stawiski/open-ring/images/charger-pcb-1.jpg

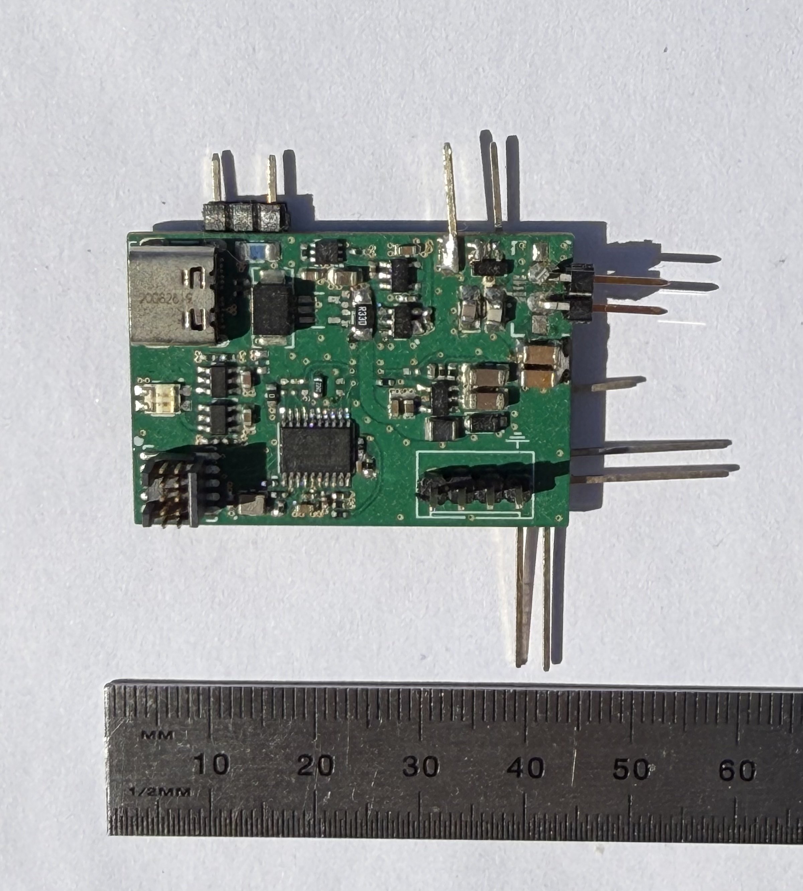
images/charger-pcb-1.jpg
