stawiski/open-ring/images/charger-pcb-2.jpg

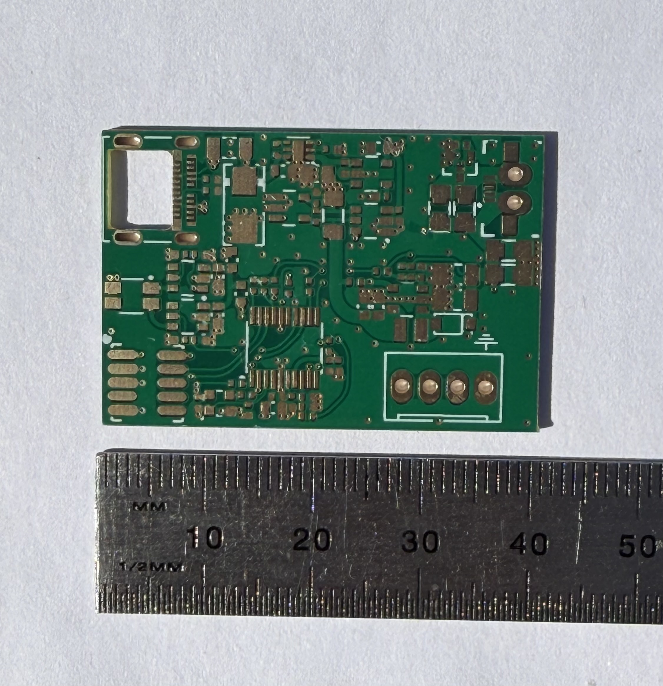
images/charger-pcb-2.jpg
