stawiski/open-ring/images/prototype-charger-2.jpg

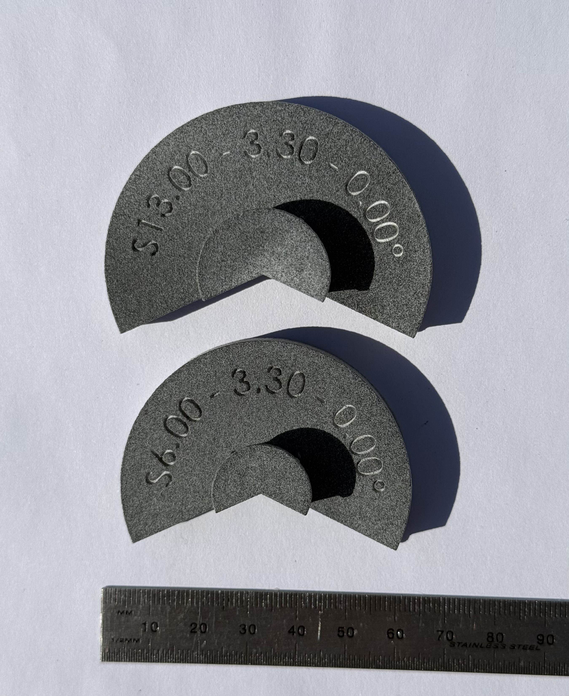
images/prototype-charger-2.jpg
