stawiski/open-ring/images/ring-antenna-w3008.jpg

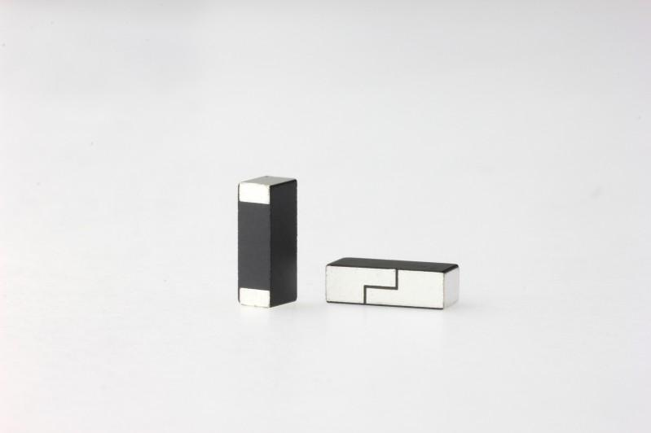
images/ring-antenna-w3008.jpg
