stawiski/open-ring/images/ring-battery-grepow-1.png

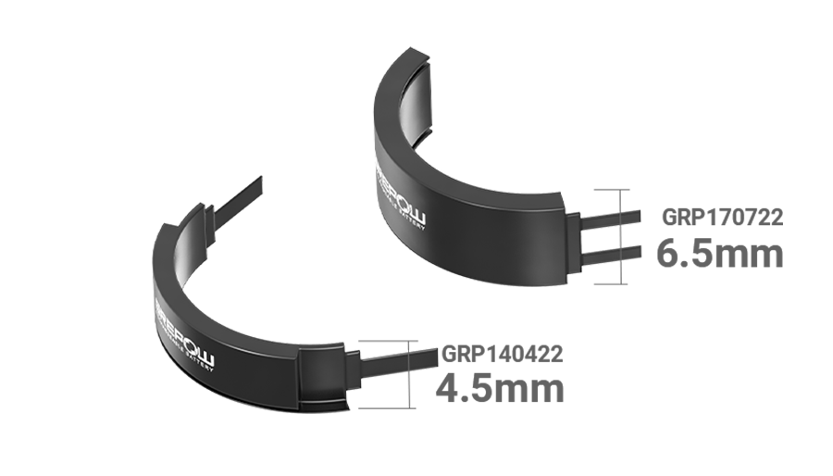
images/ring-battery-grepow-1.png
