stawiski/open-ring/images/ring-battery-grepow-2.jpg

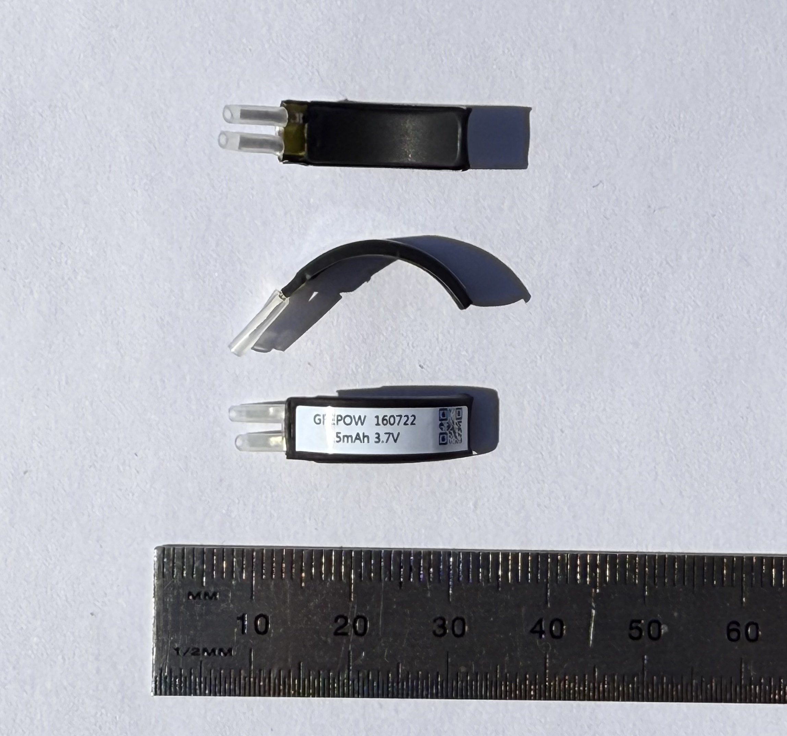
images/ring-battery-grepow-2.jpg
