stawiski/open-ring/images/ring-touch-sensor-prototypes-1.png

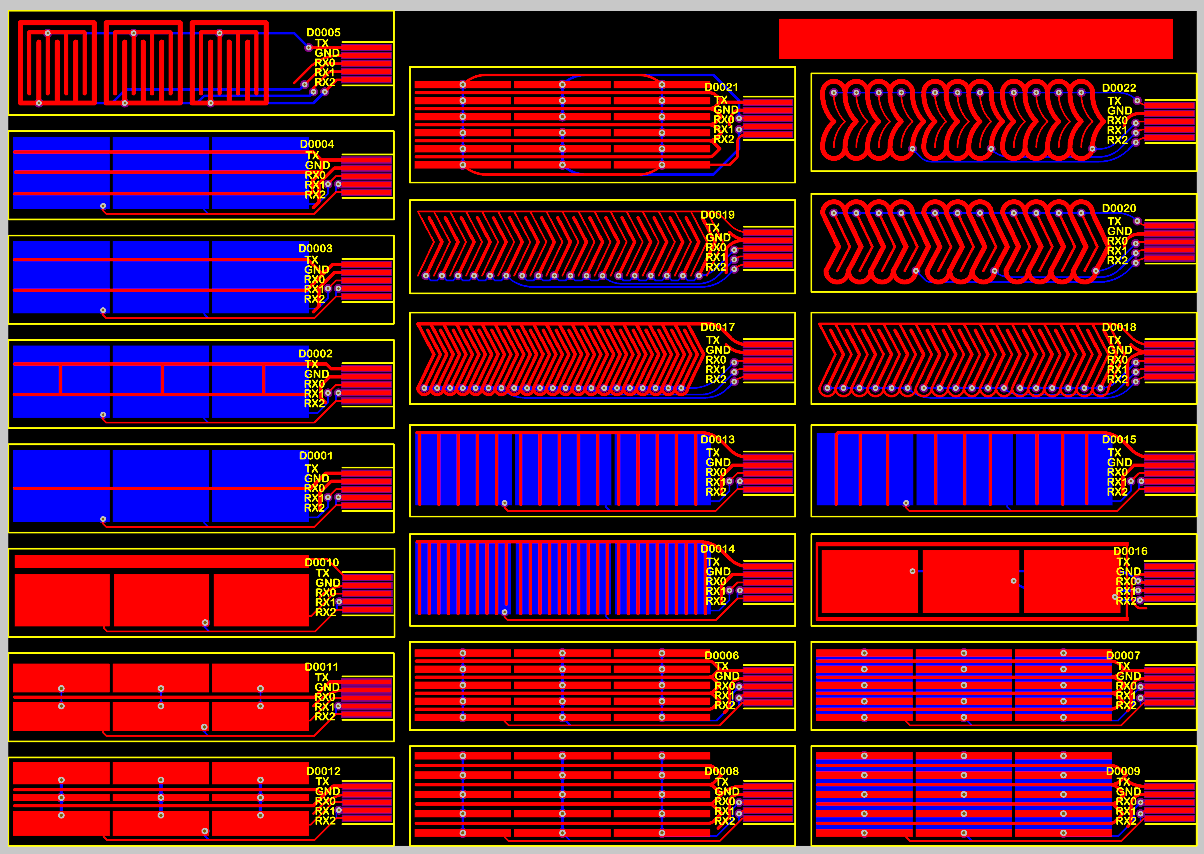
images/ring-touch-sensor-prototypes-1.png
