stawiski/open-ring/hardware-prototypes/ring-dev-board/docs/Connector Molex 545480433_sd.pdf

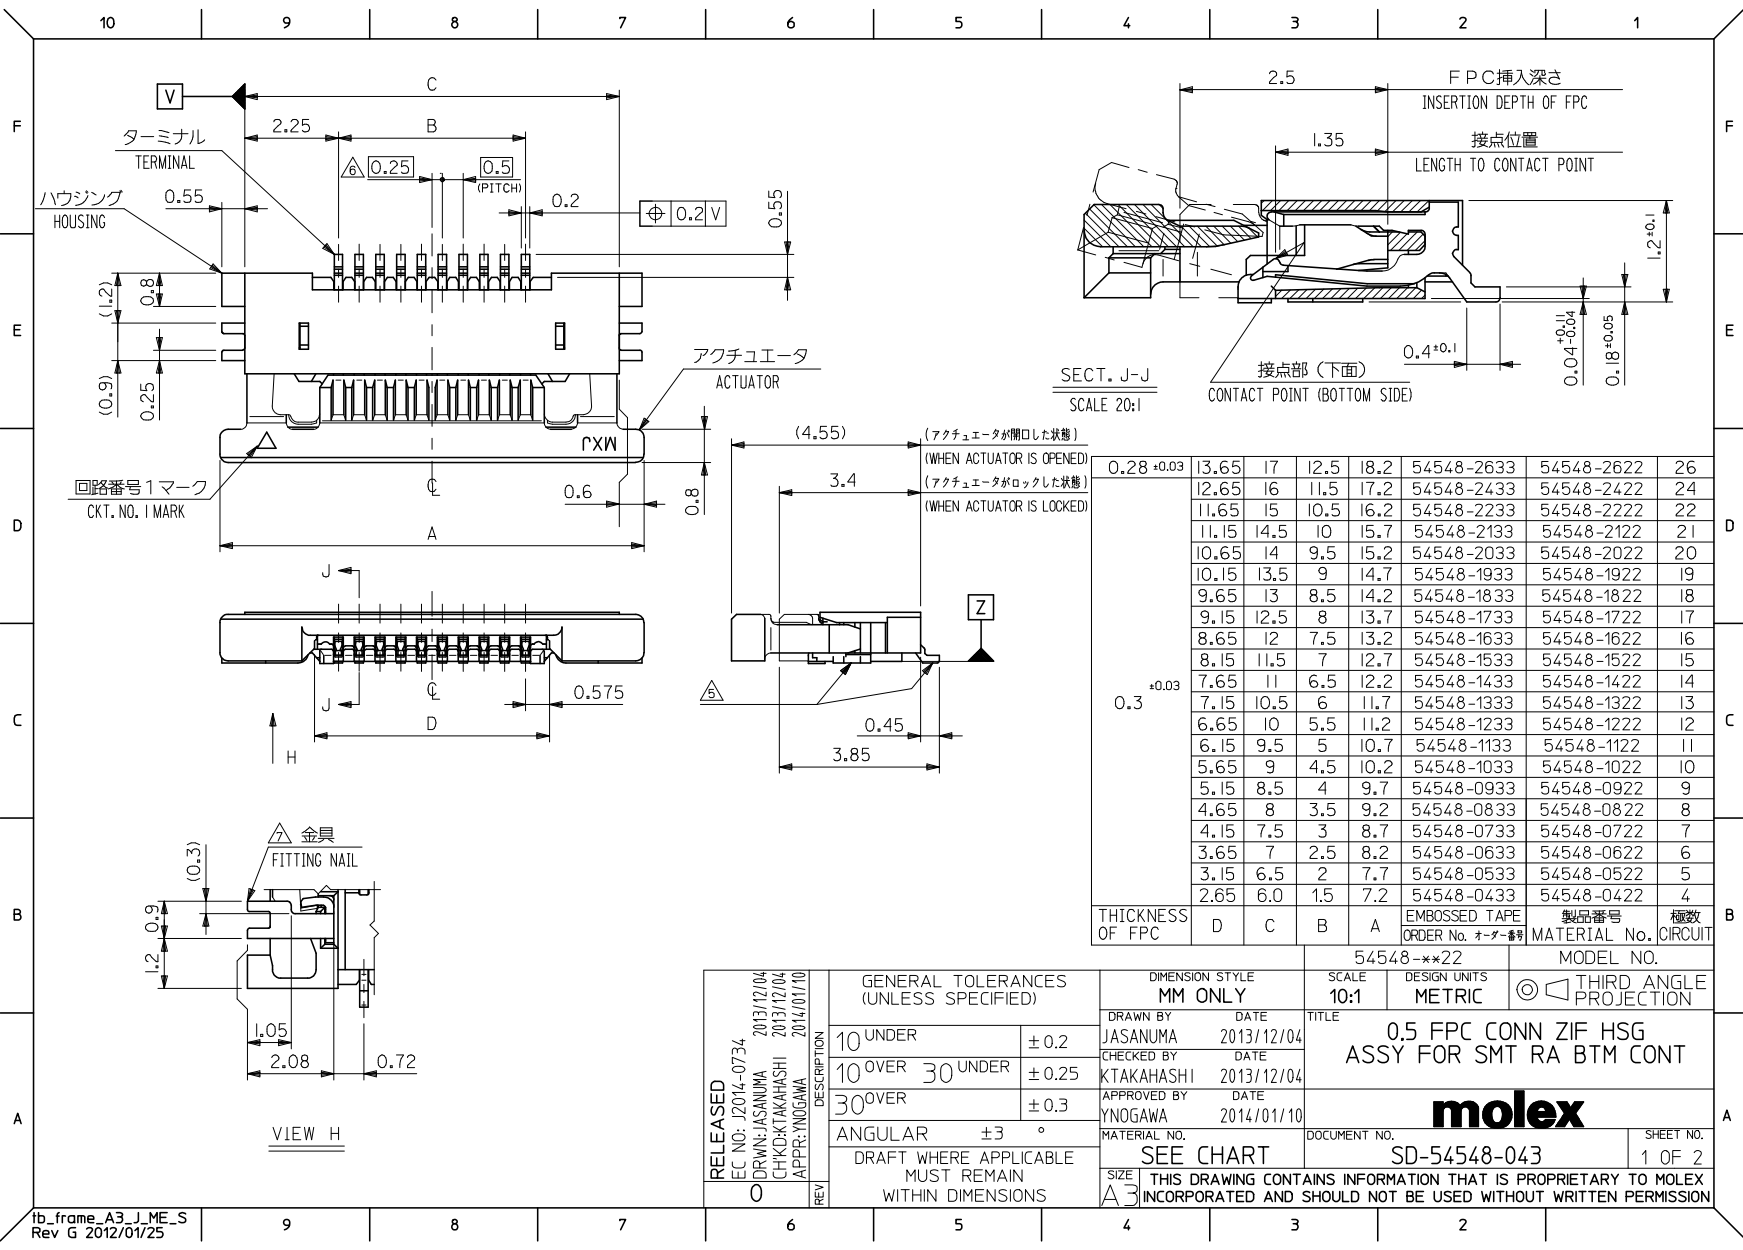
[picture p18: page 1]

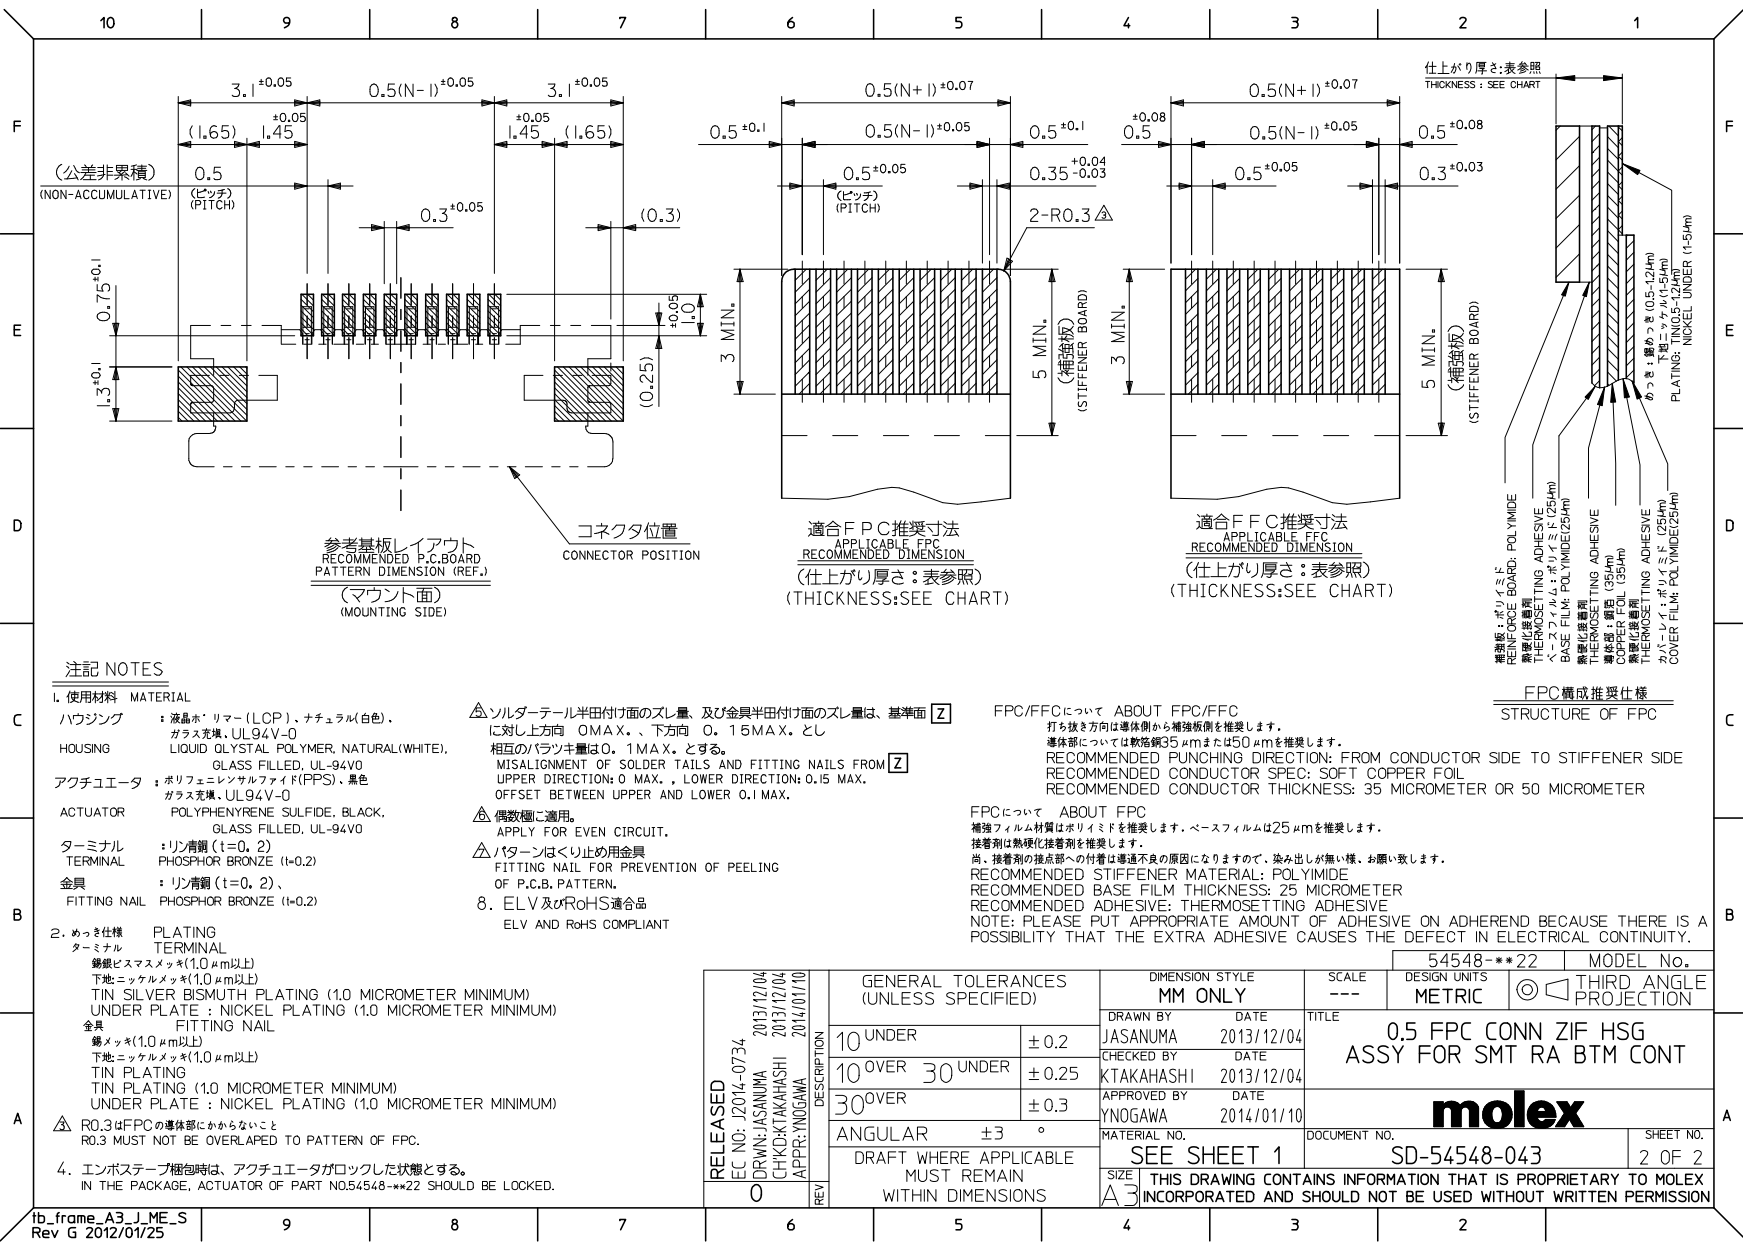
[picture p19: page 2]

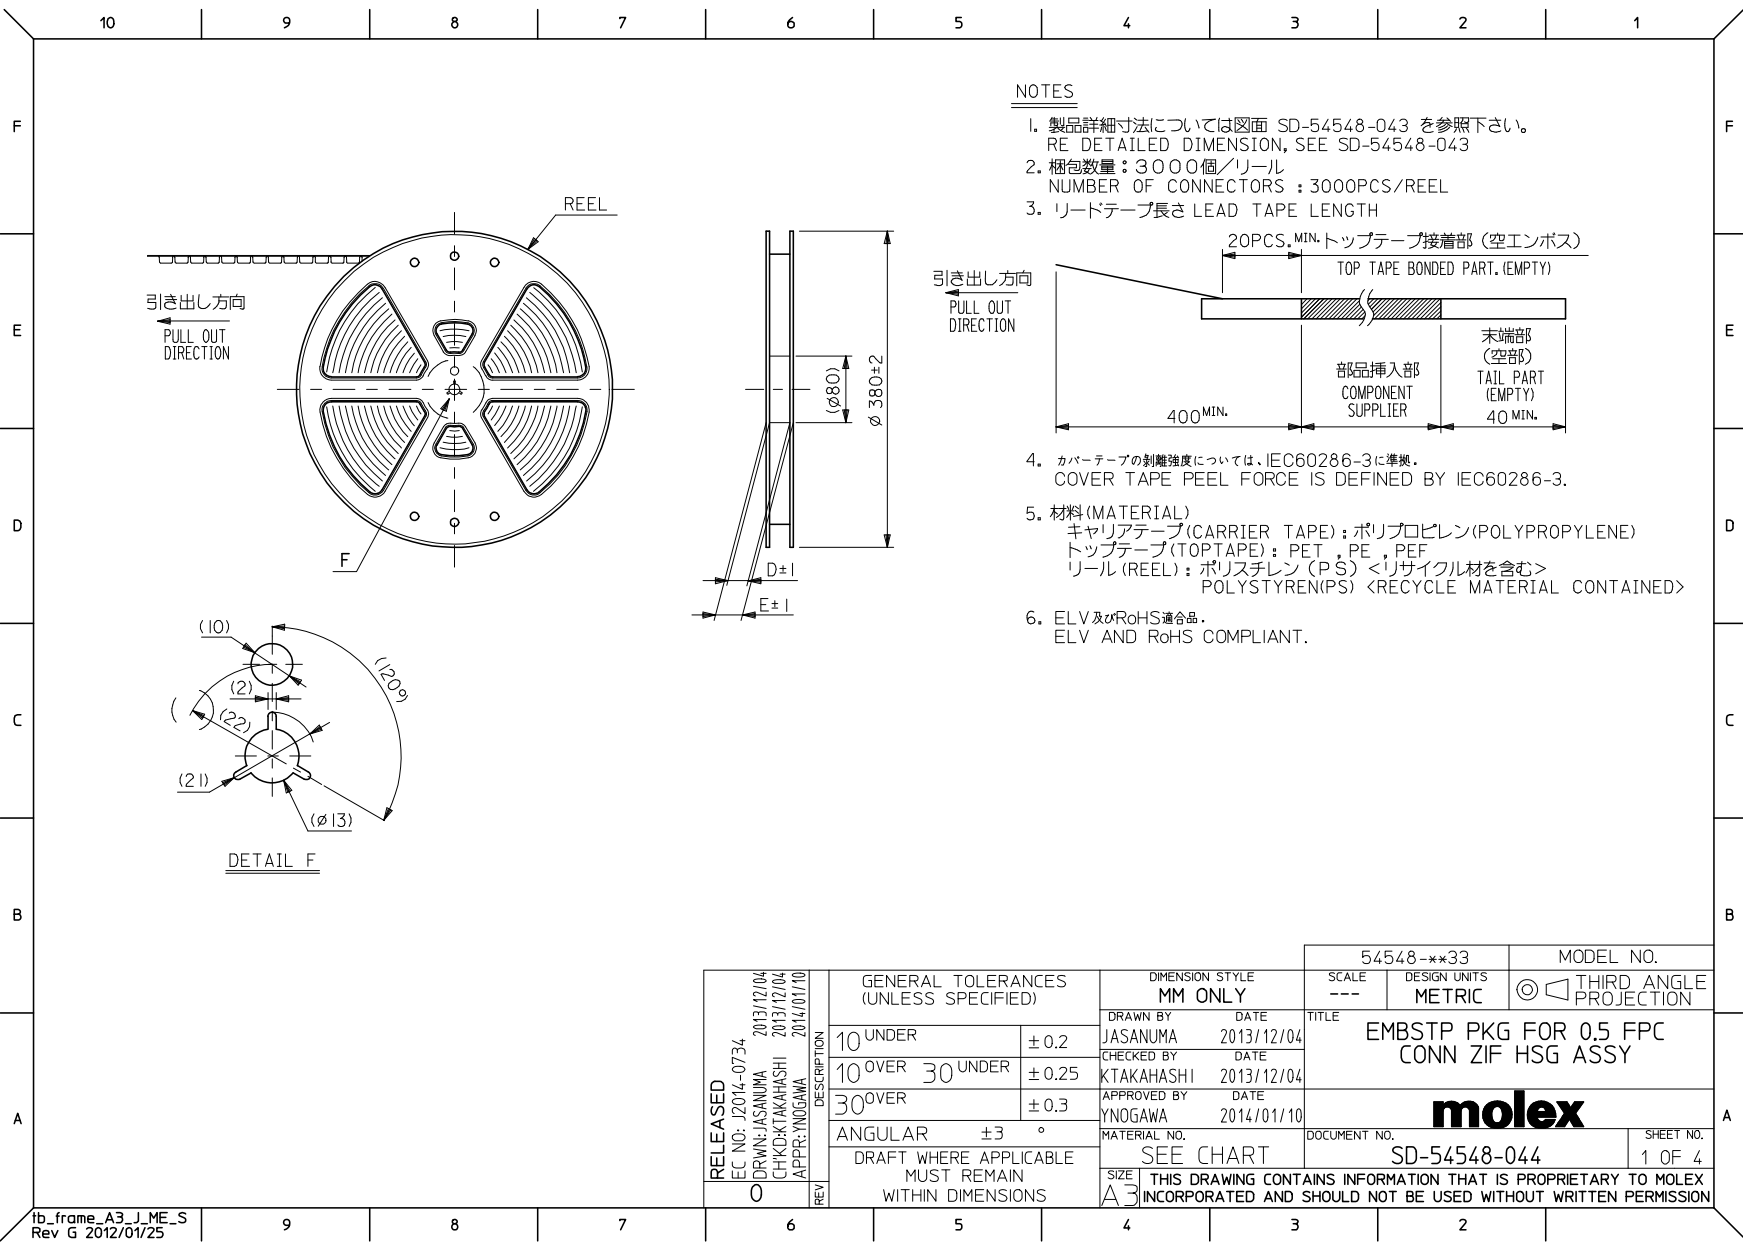
[picture p20: page 3]

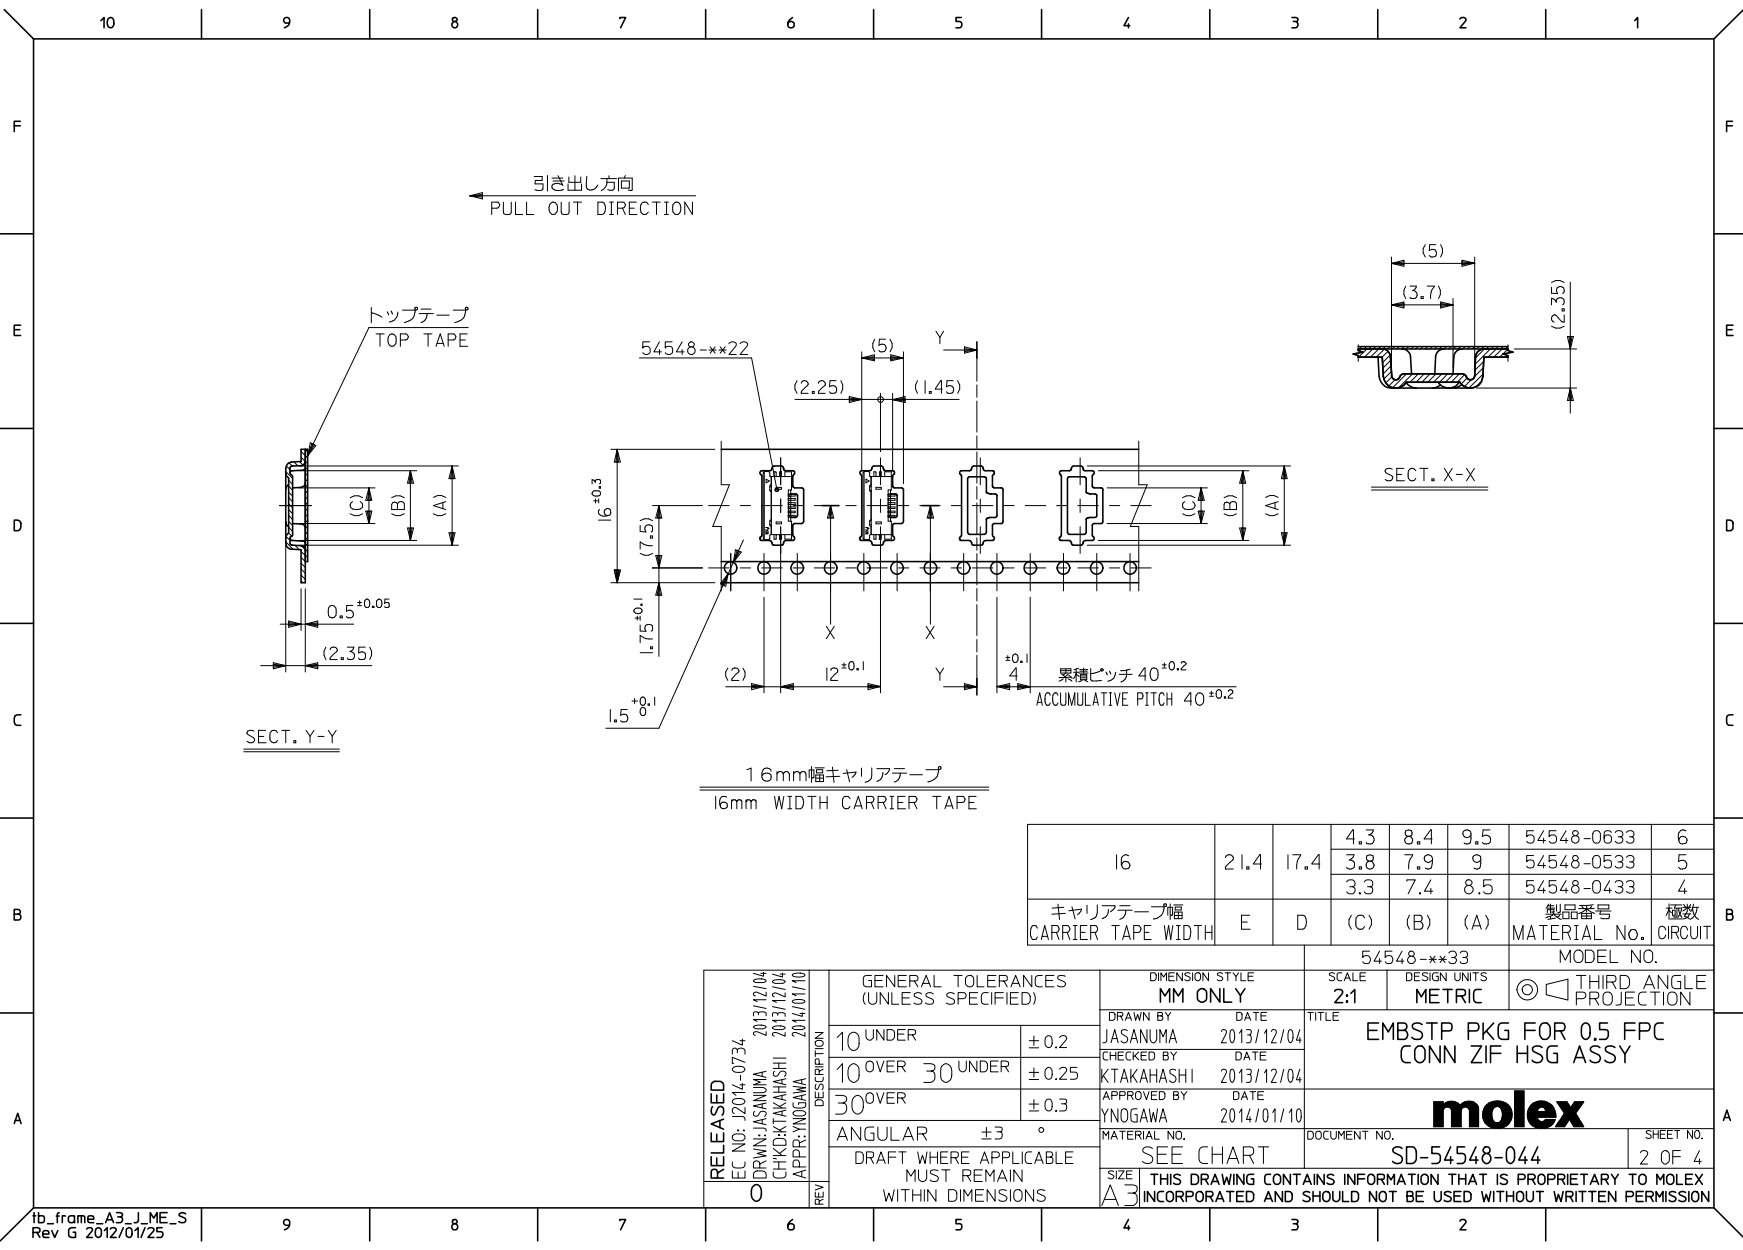
[picture p21: page 4]

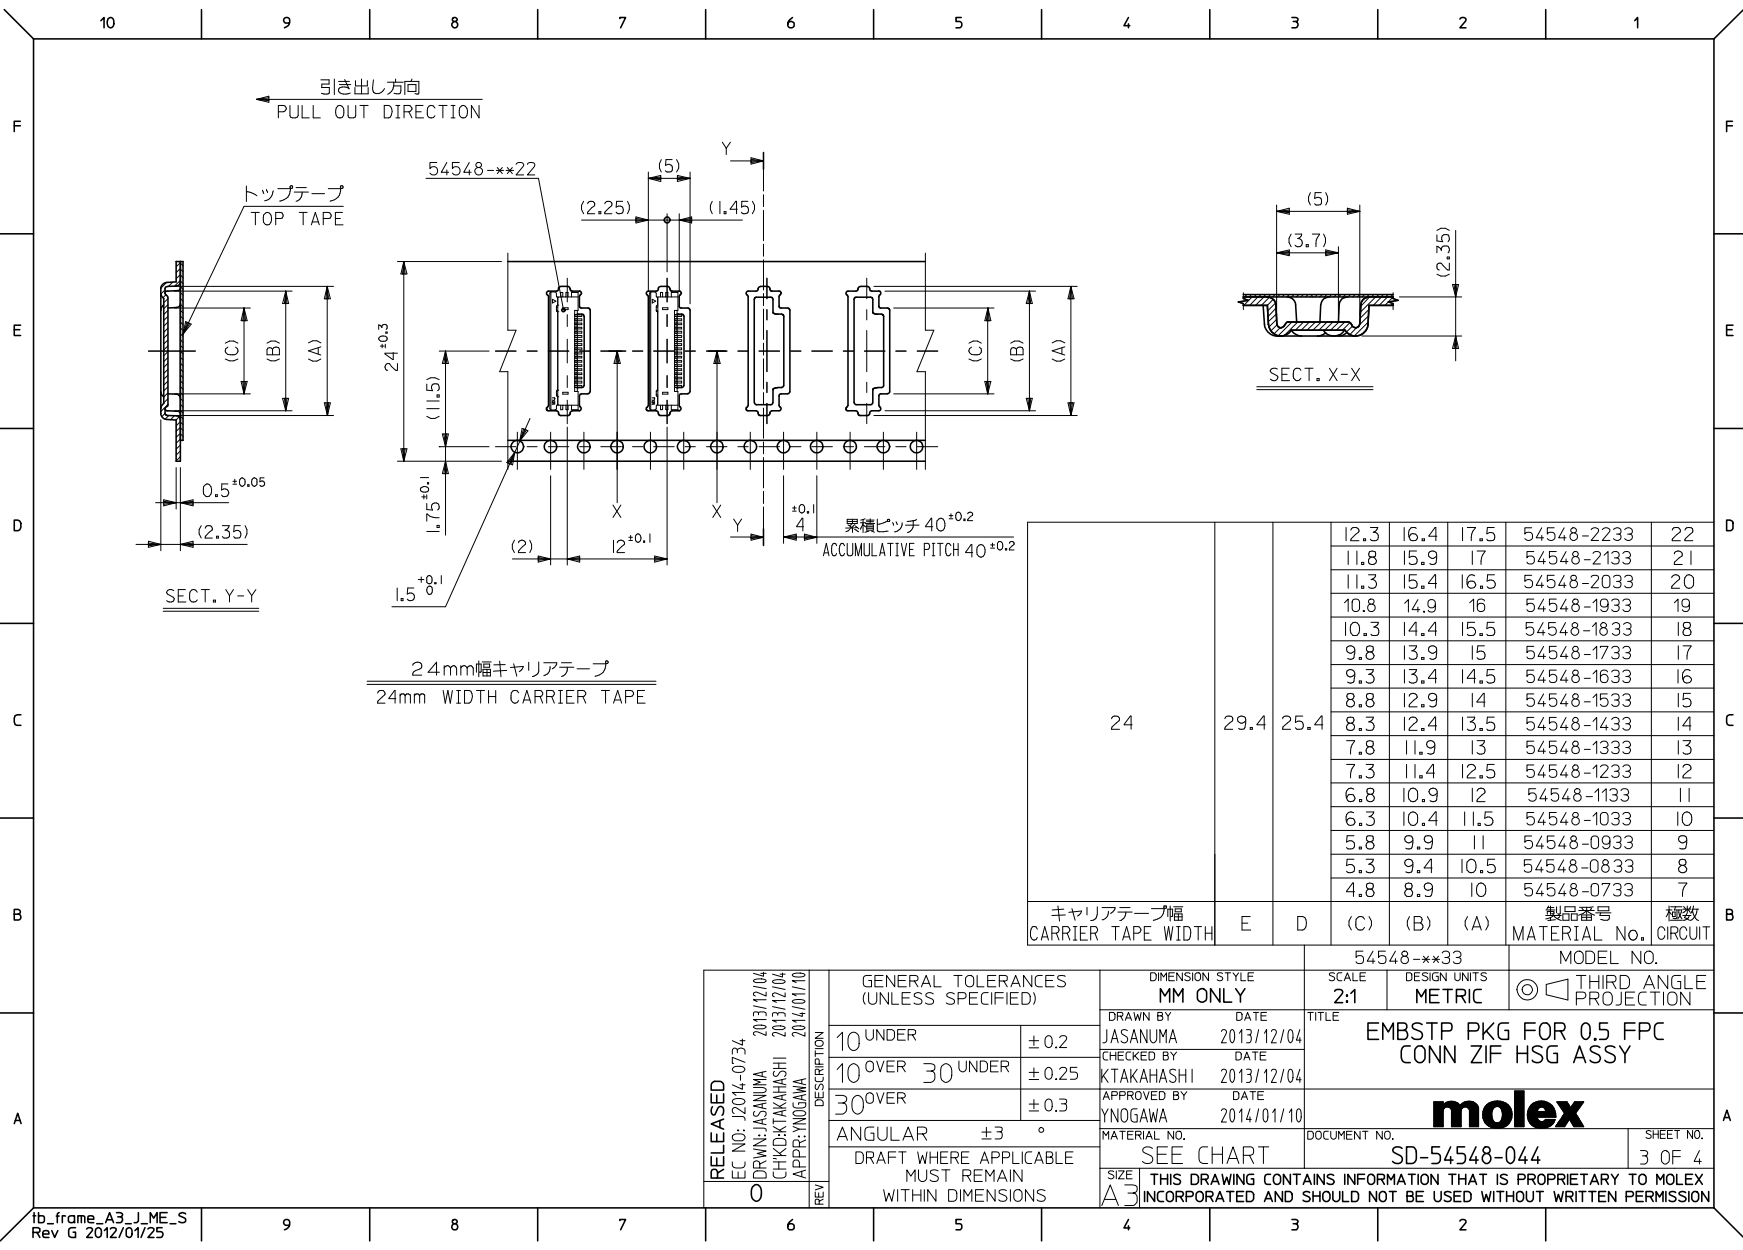
[picture p22: page 5]

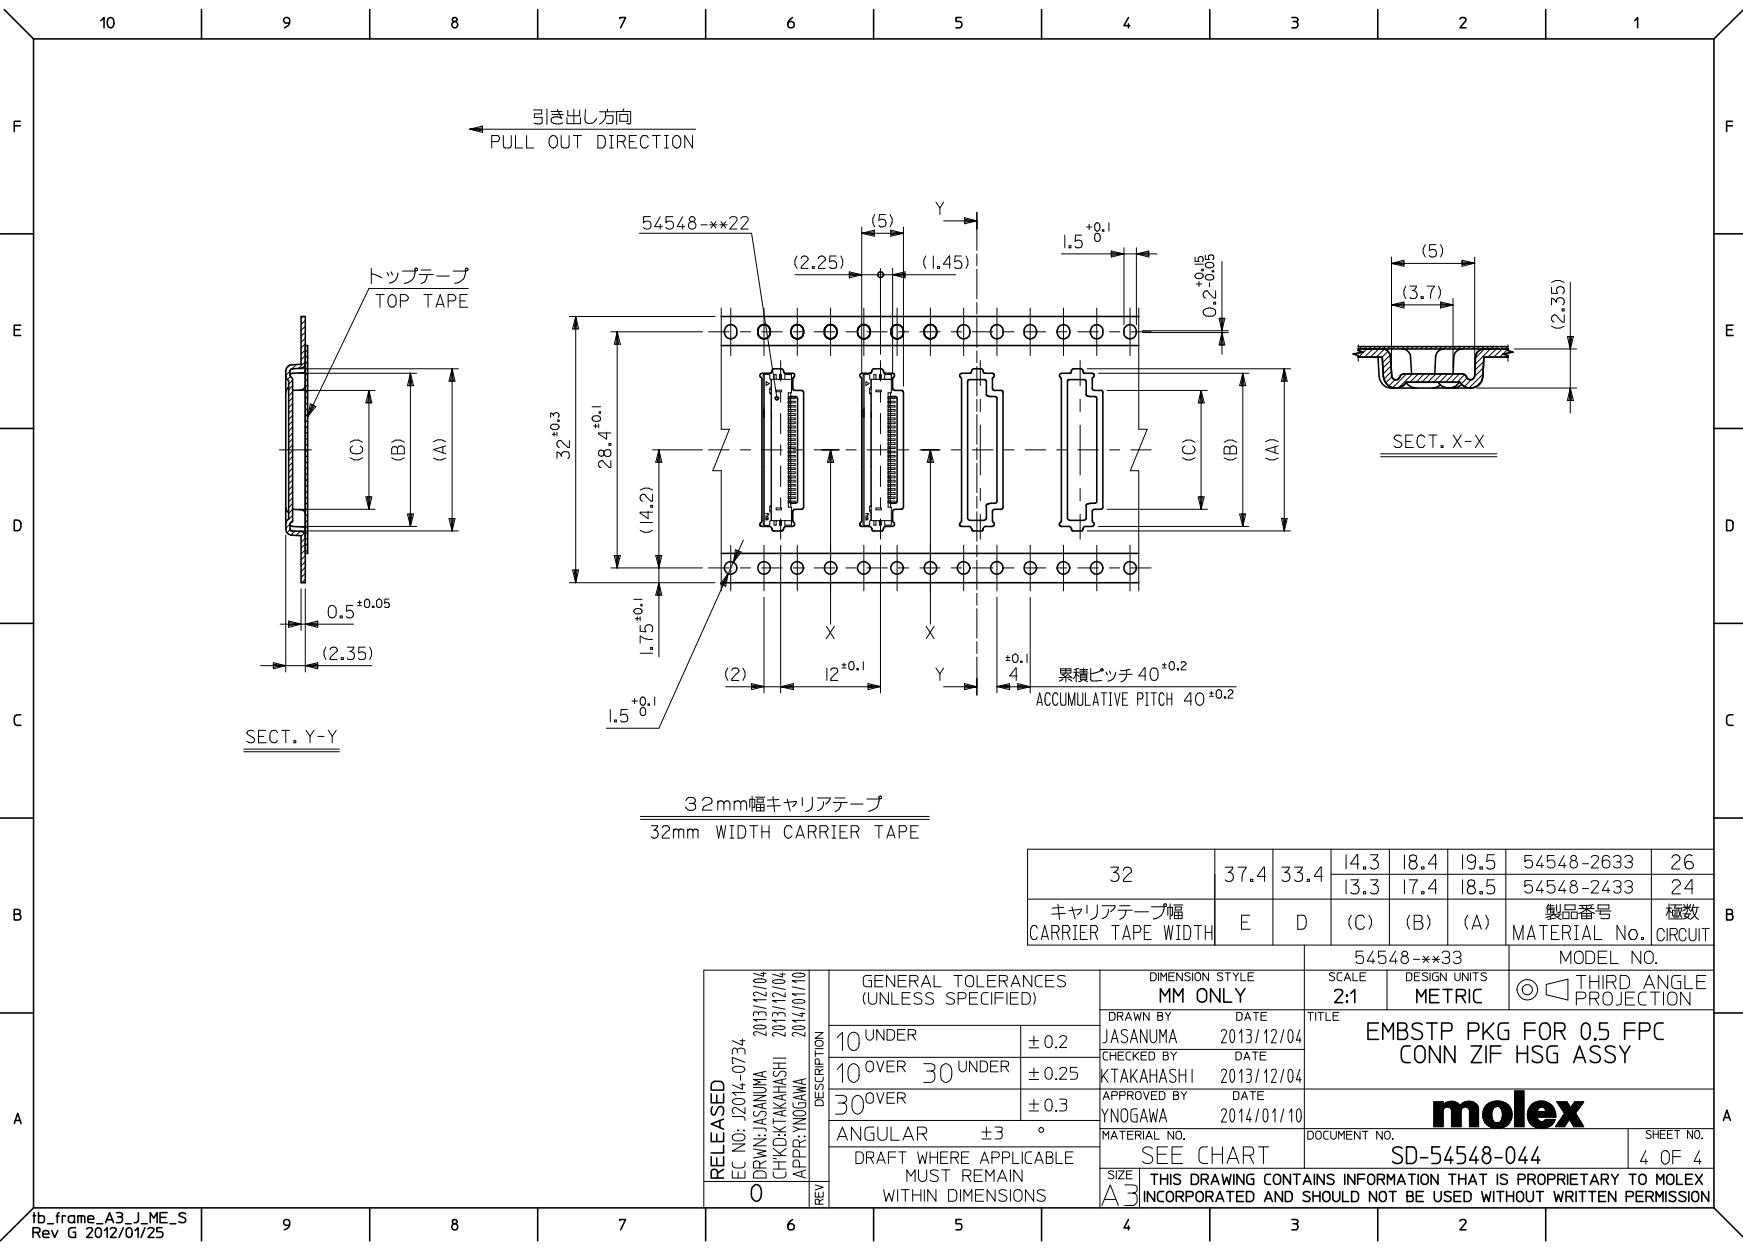
[picture p23: page 6]
