stawiski/open-ring/hardware-prototypes/ring-dev-board/docs/Connector Molex 545502671_sd.pdf

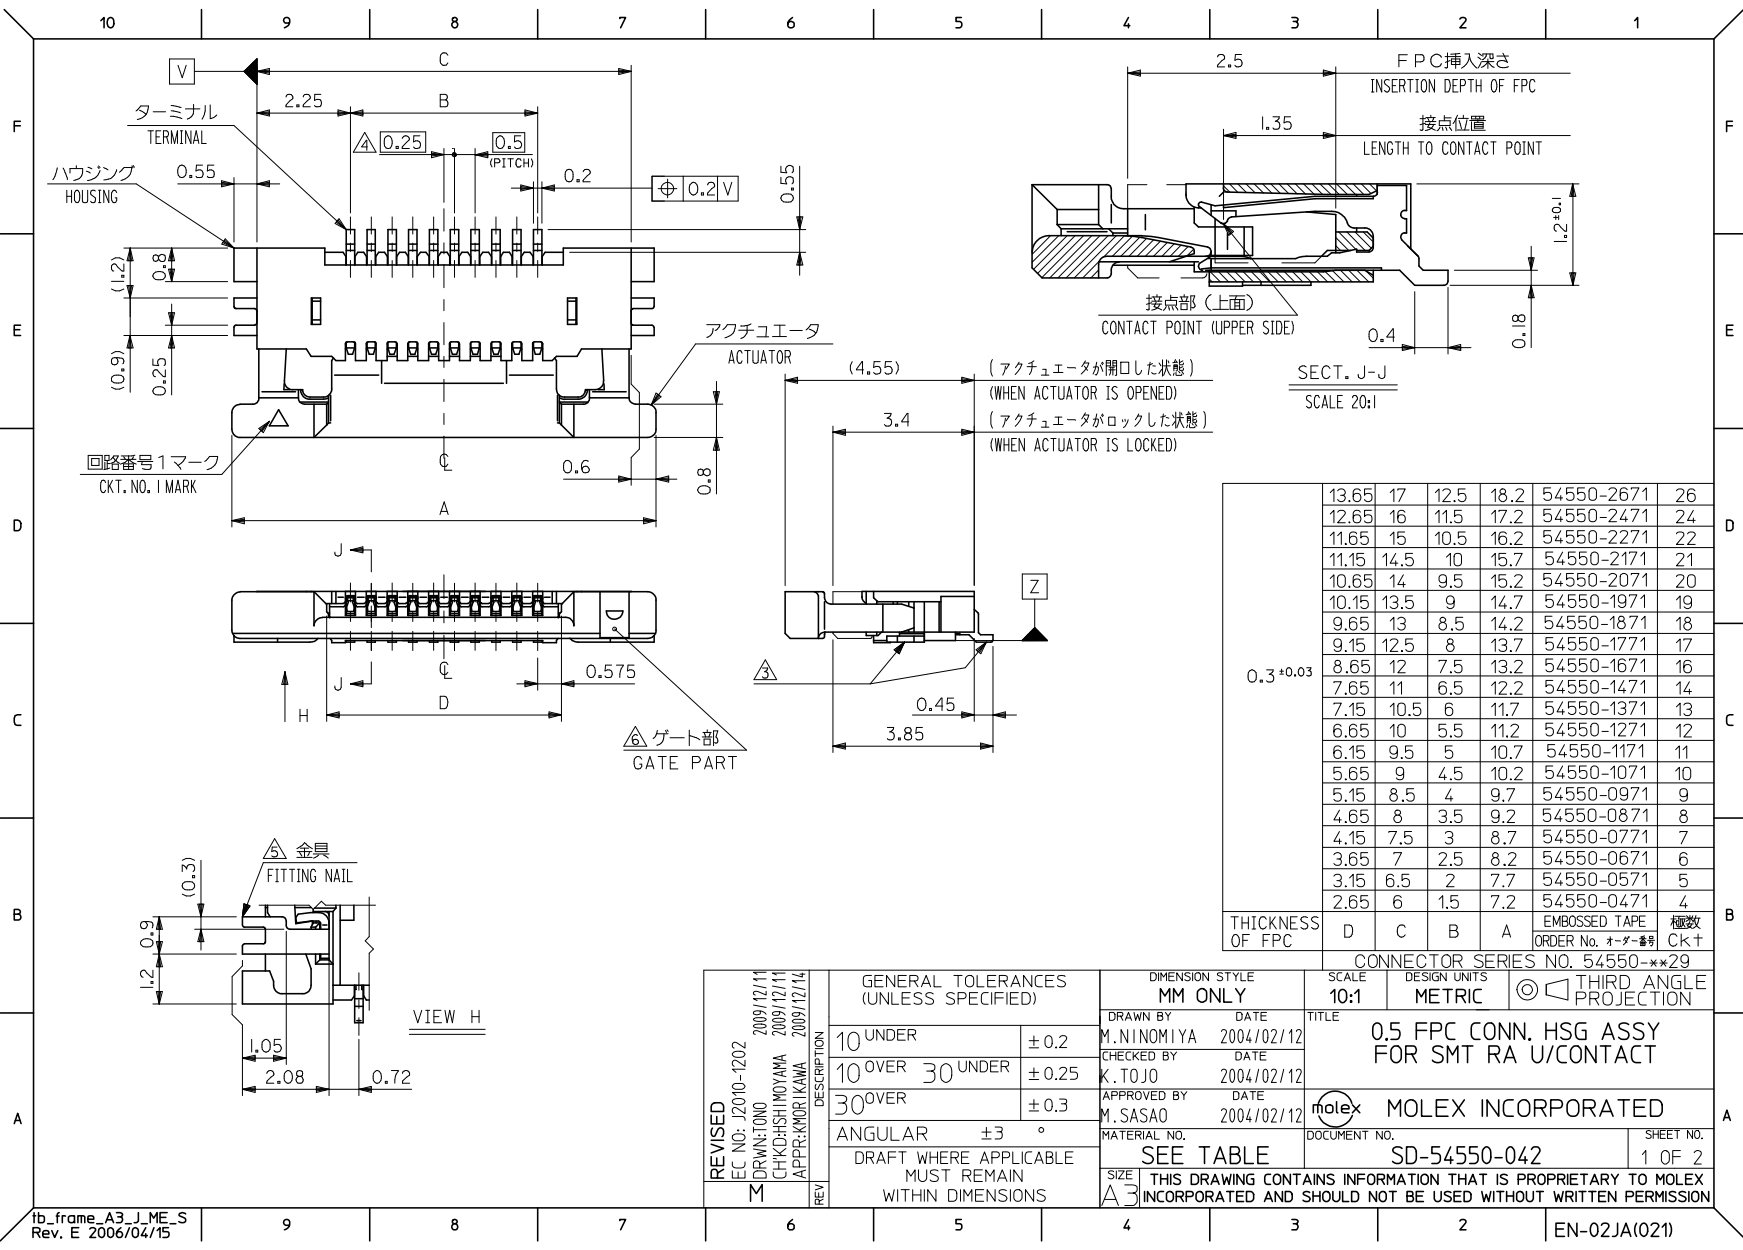
[picture p24: page 1]

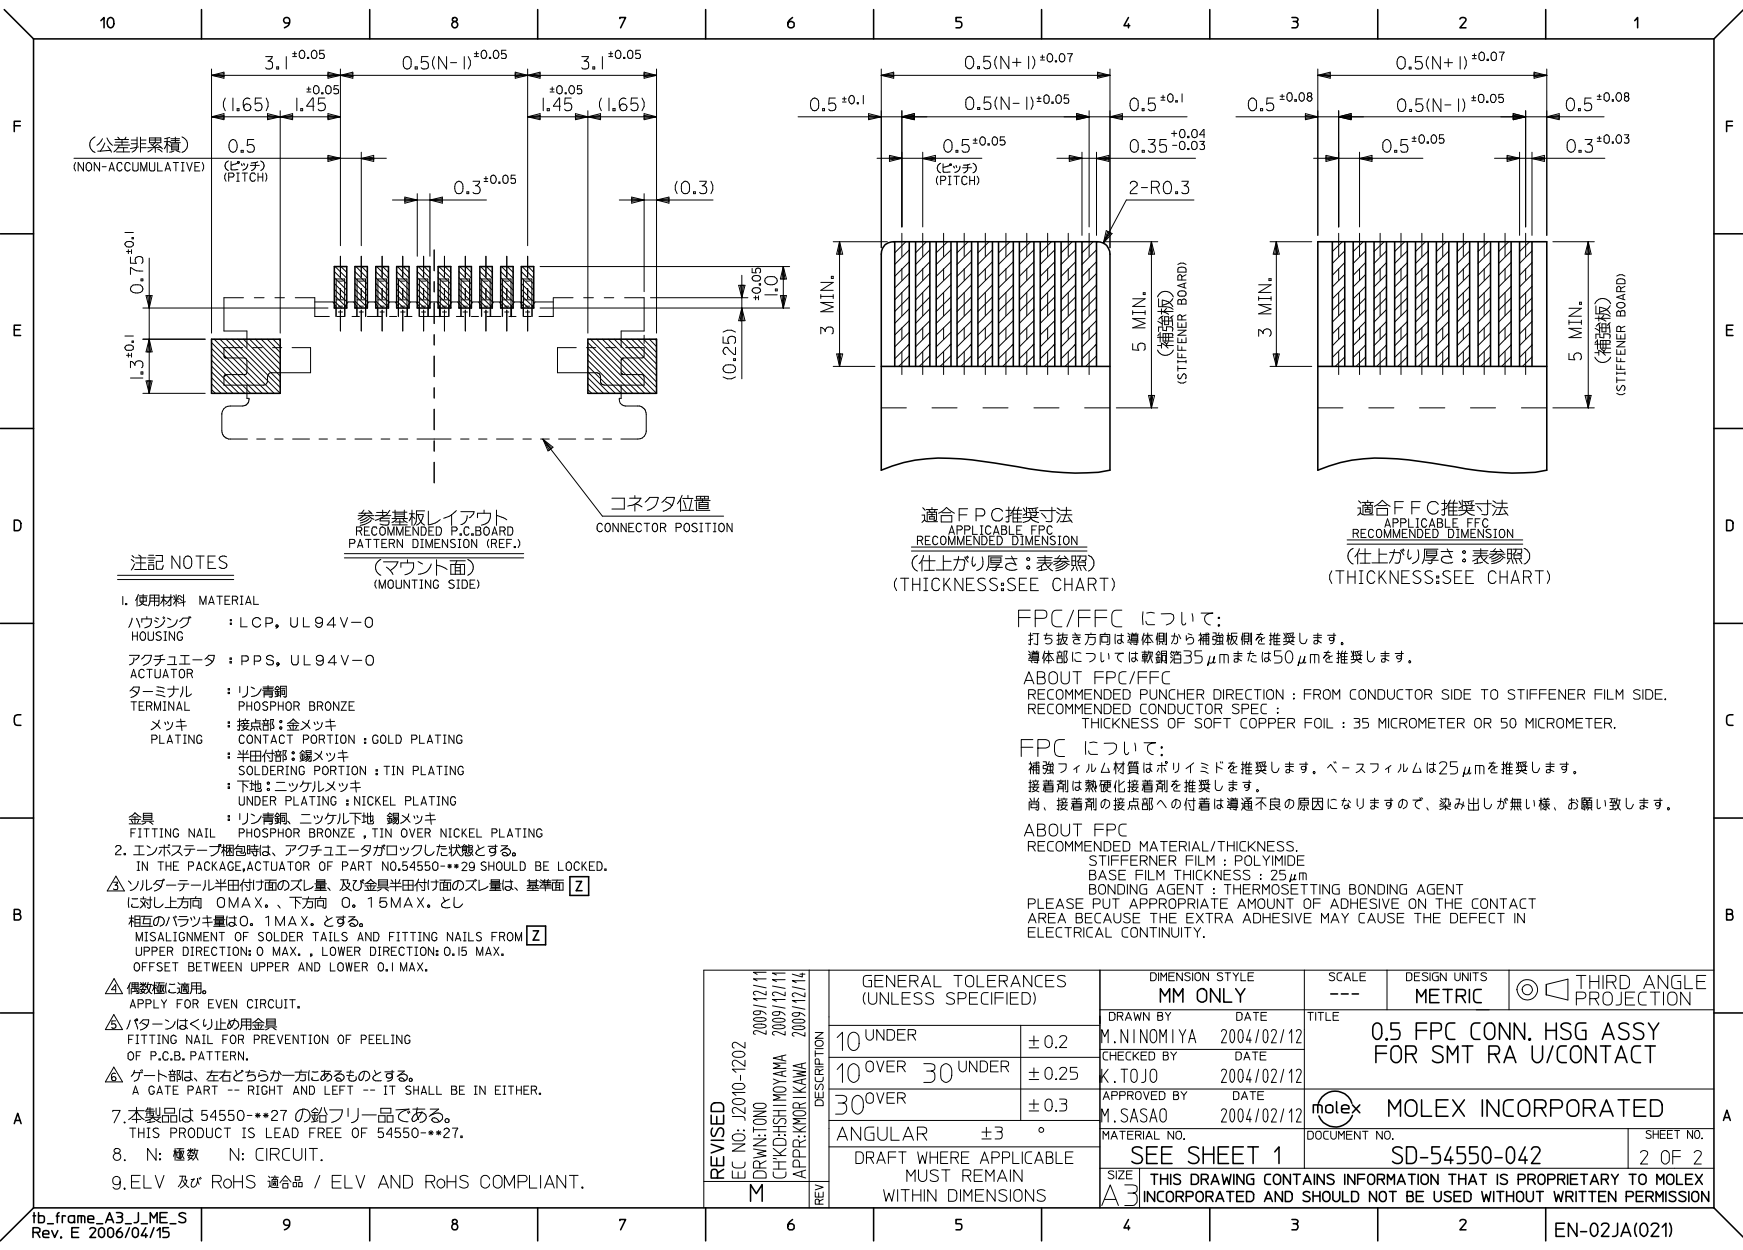
[picture p25: page 2]

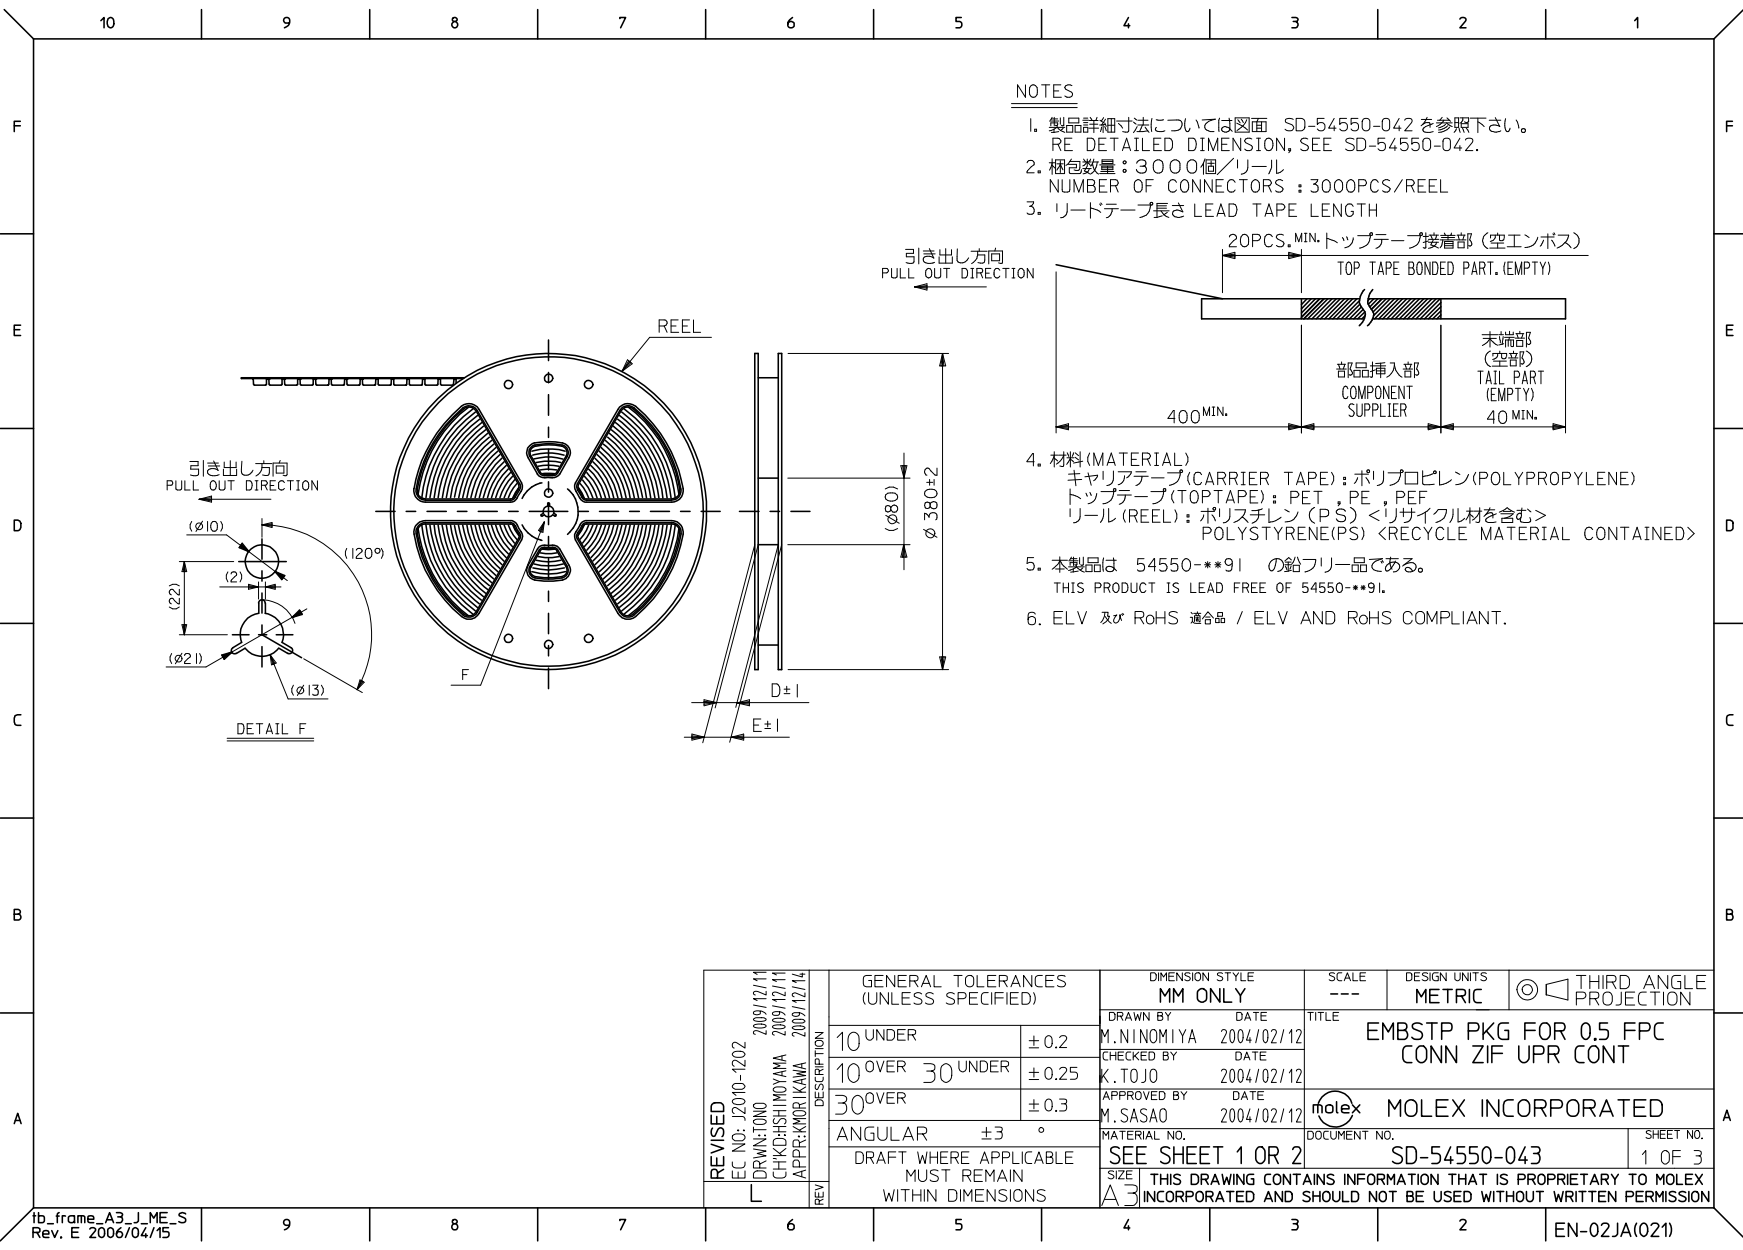
[picture p26: page 3]

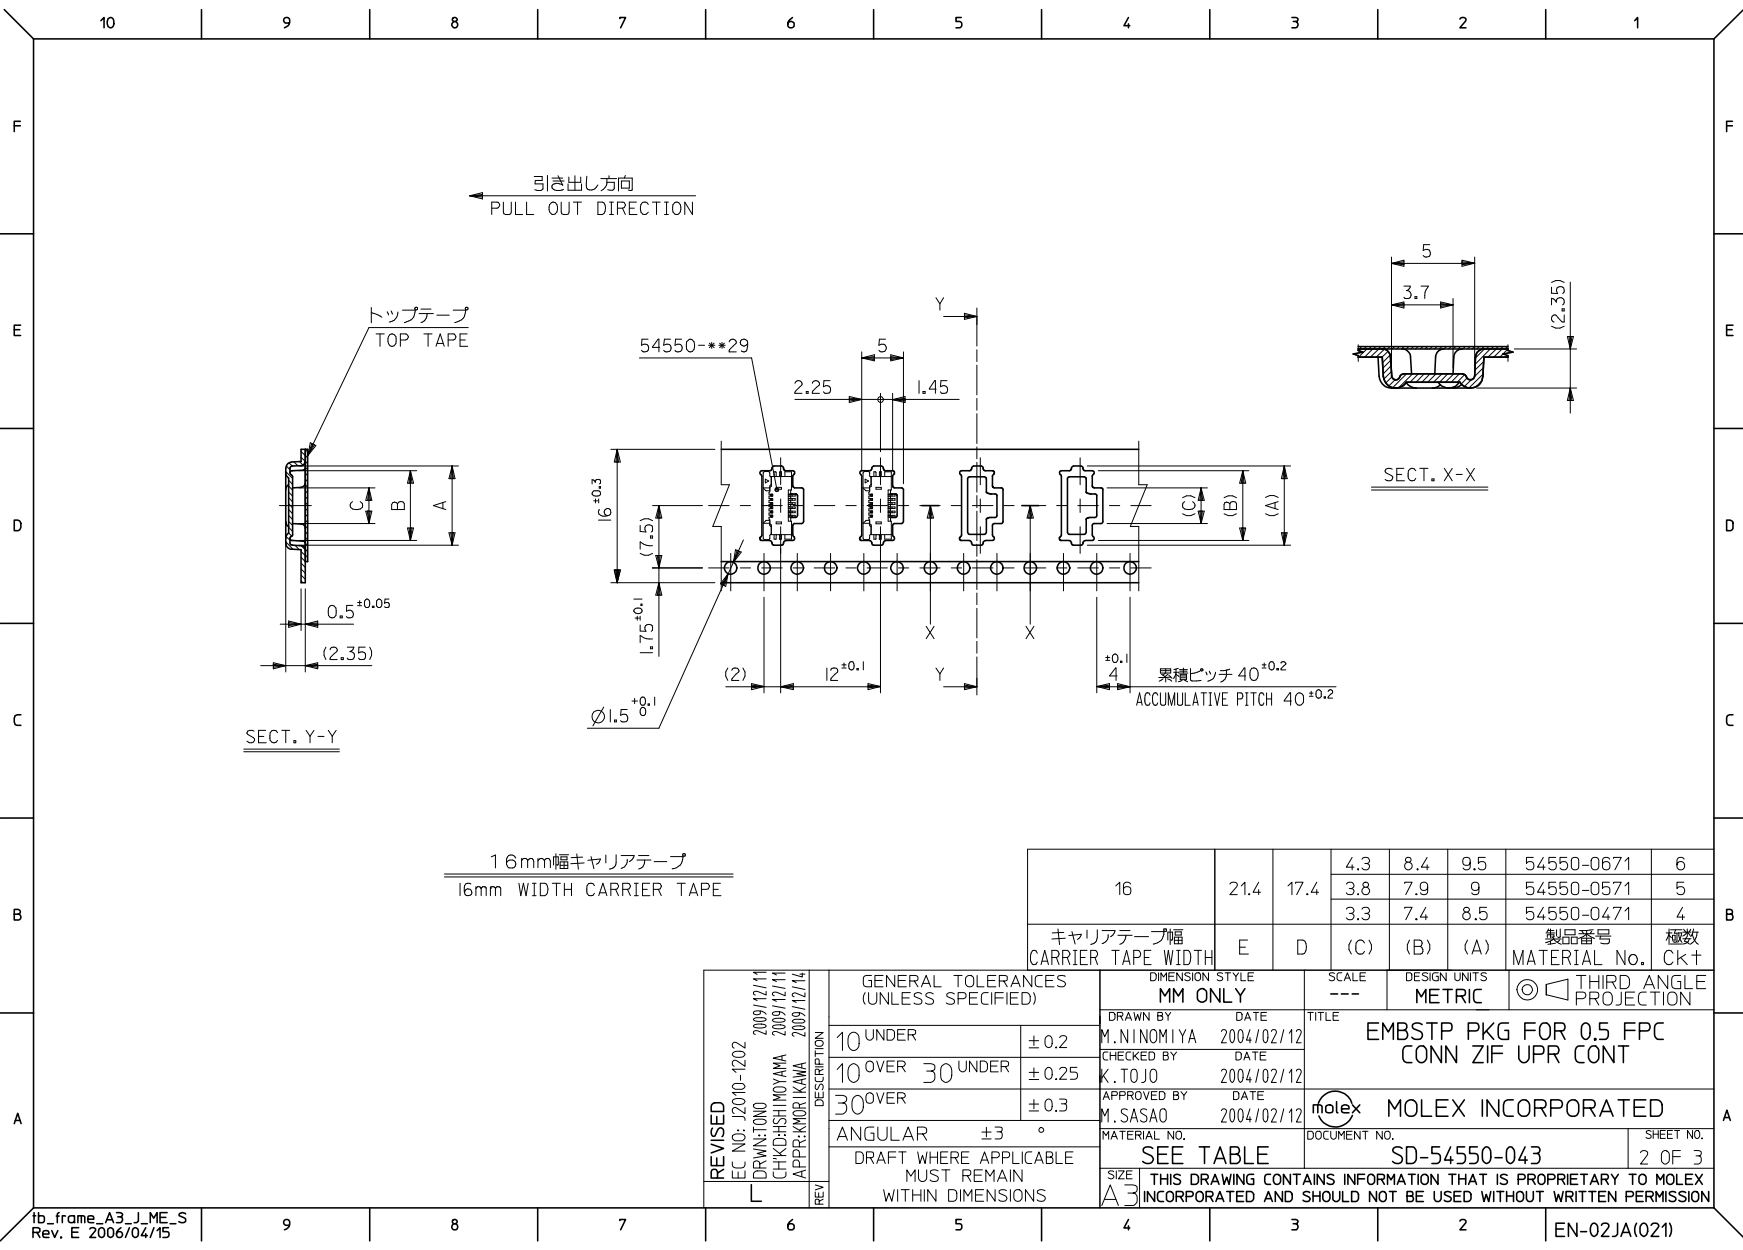
[picture p27: page 4]

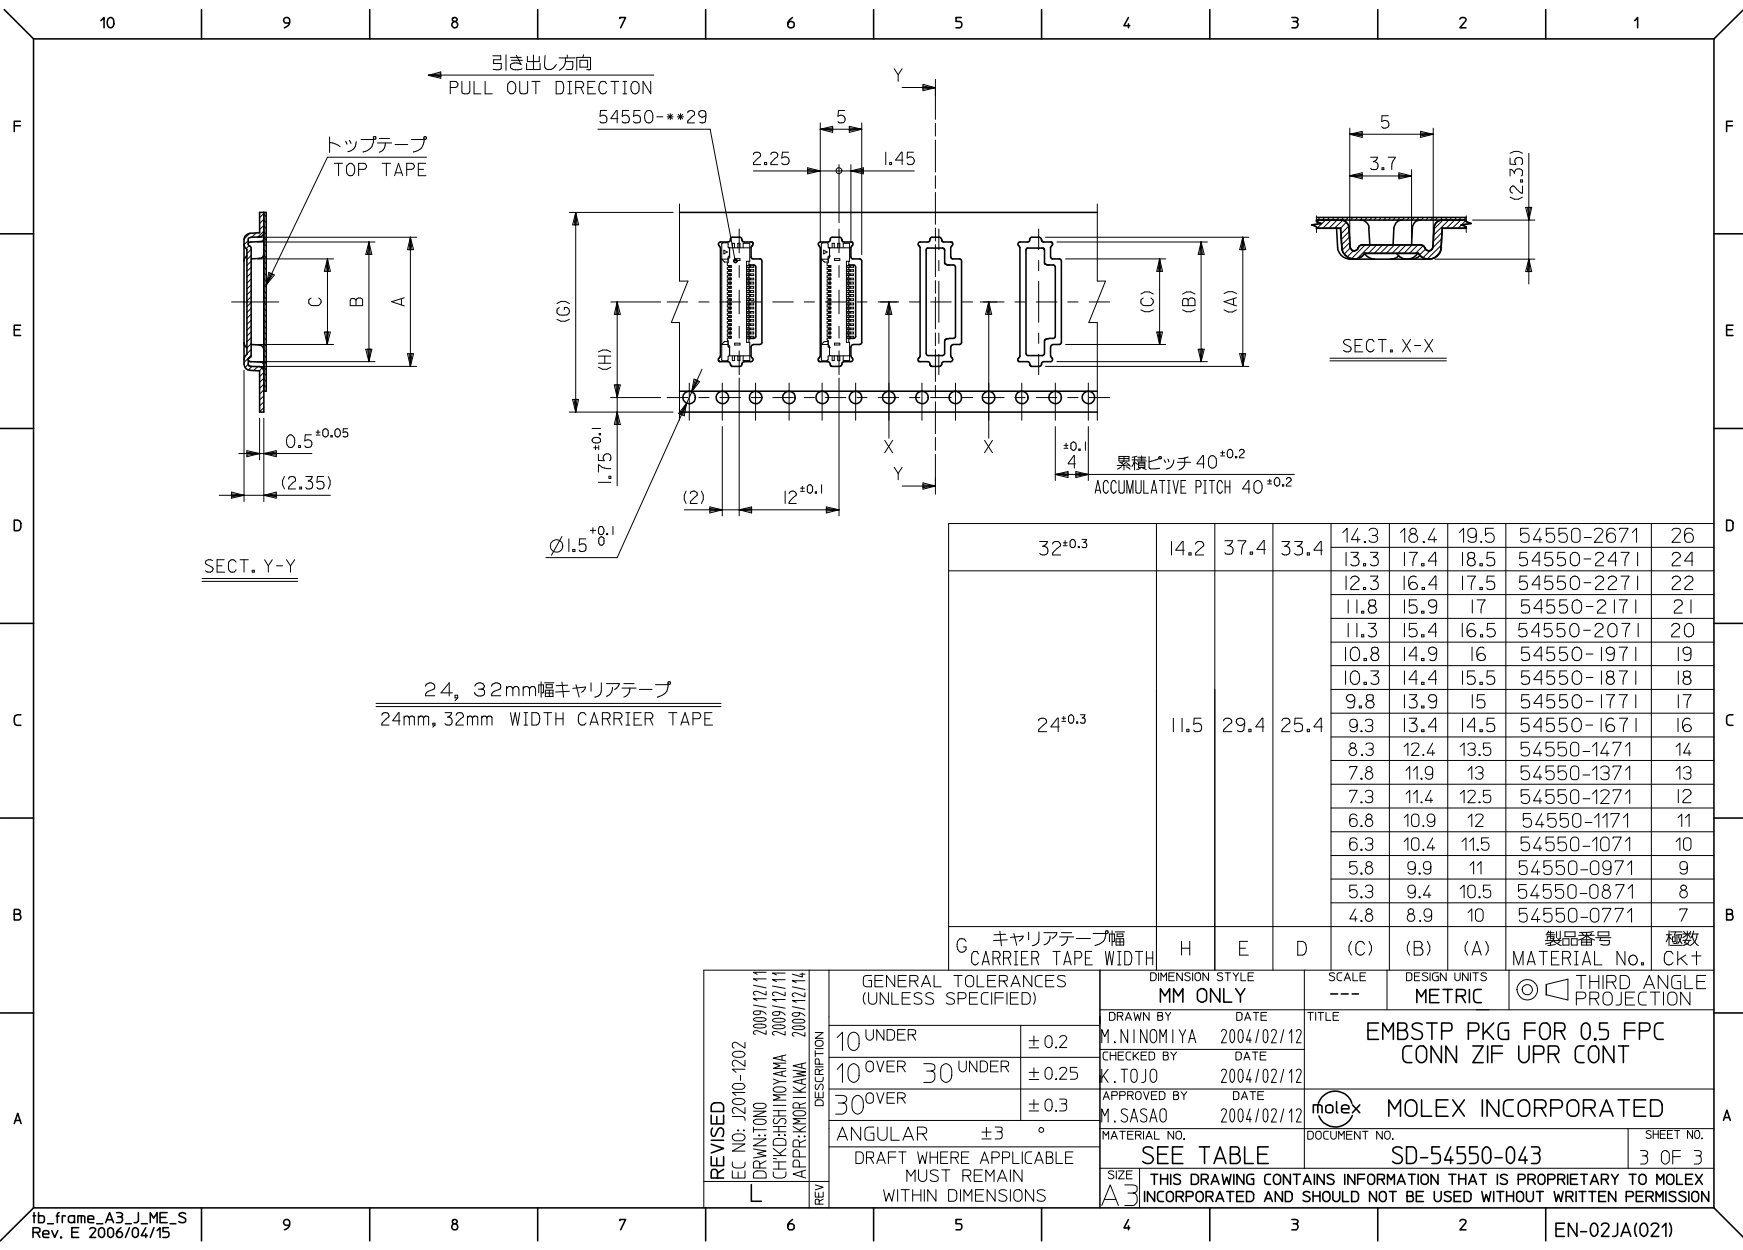
[picture p28: page 5]
