stawiski/open-ring/hardware-prototypes/ring-dev-board/example-dialog-dev-board/DA14531-devkt-b-usb_vC3_(376-13-C)-PCB.pdf

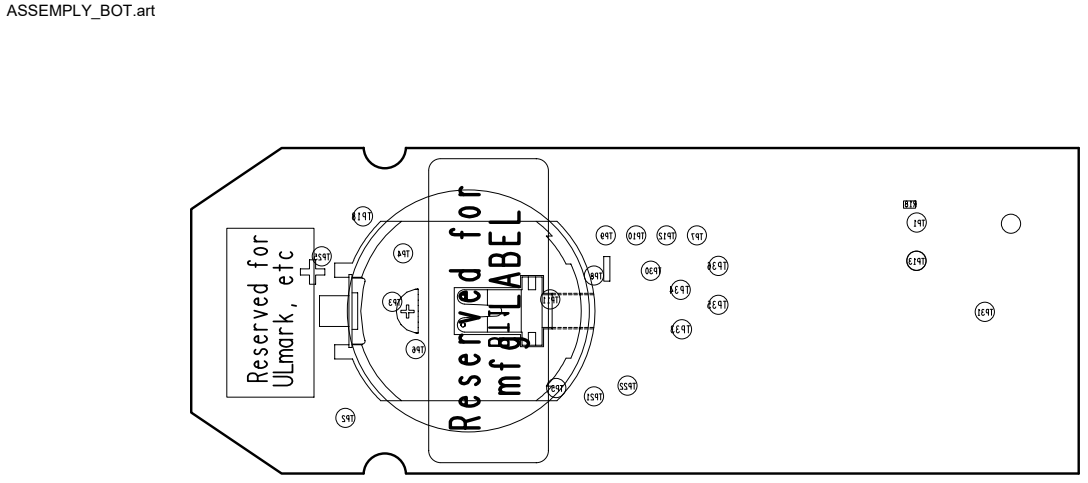
[picture p29: page 1]
ASSEMPLY_BOT.art

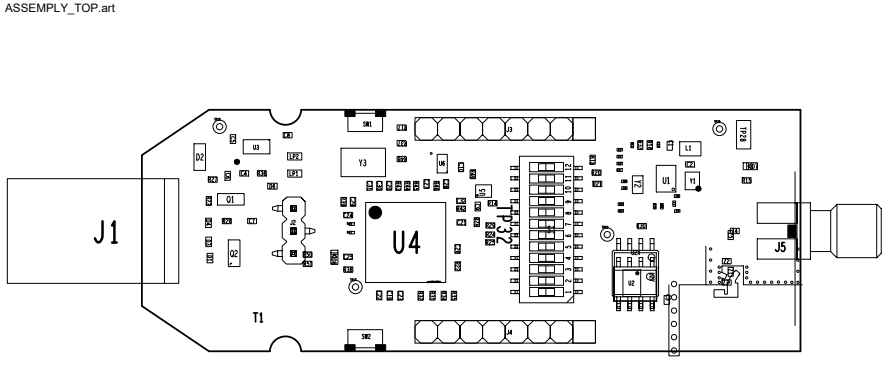
[picture p30: page 2]
ASSEMPLY_TOP.art

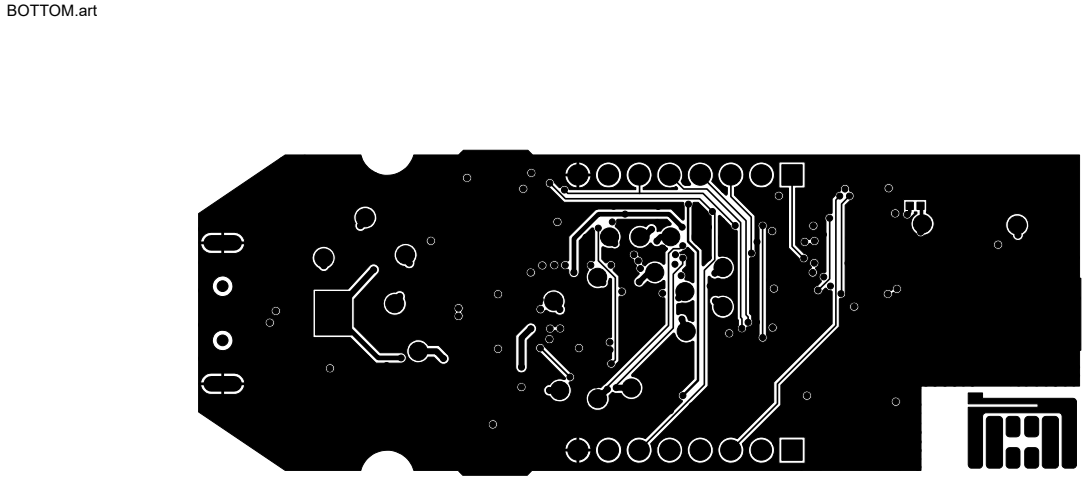
[picture p31: page 3]
BOTTOM.art

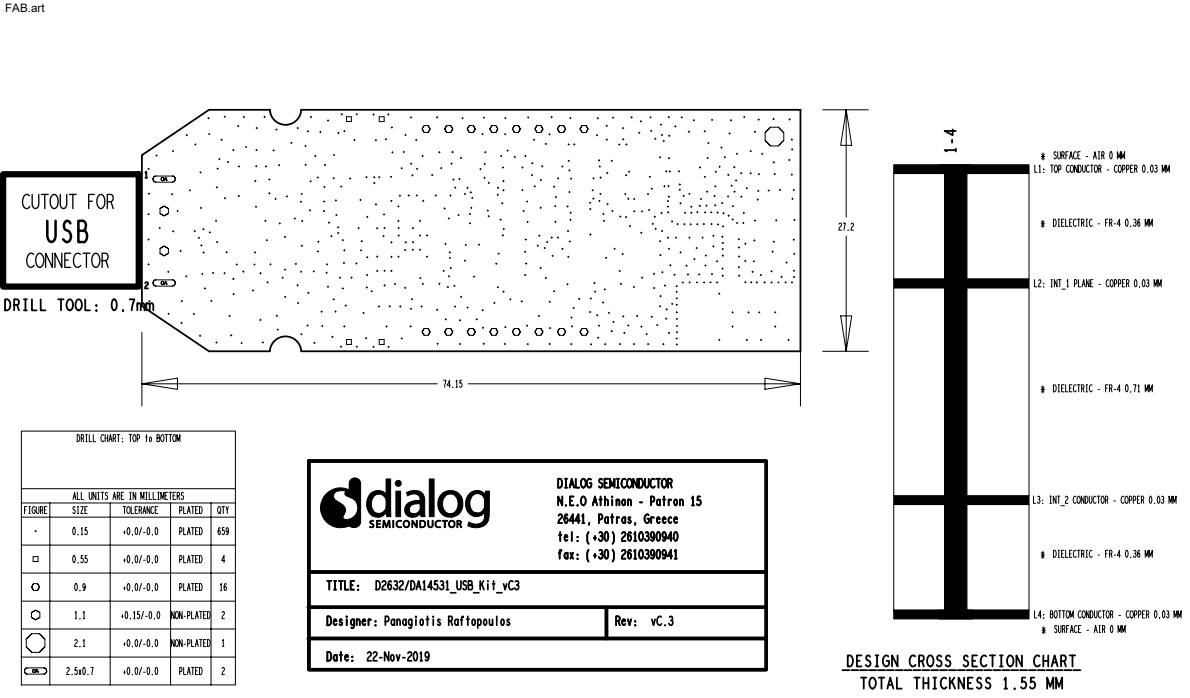
[picture p32: page 4]
FAB.art

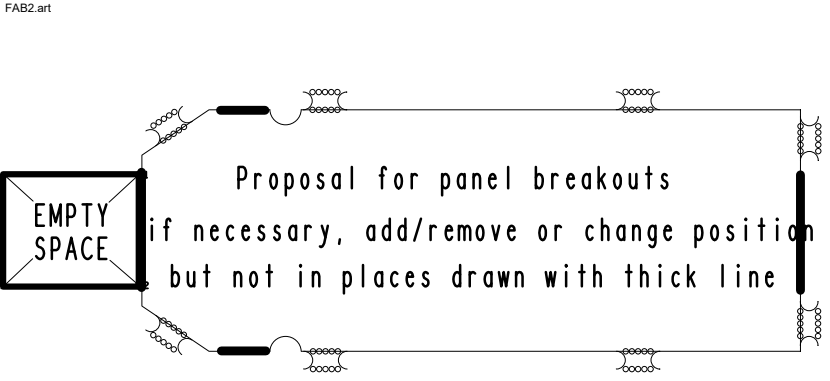
[picture p33: page 5]
FAB2.art

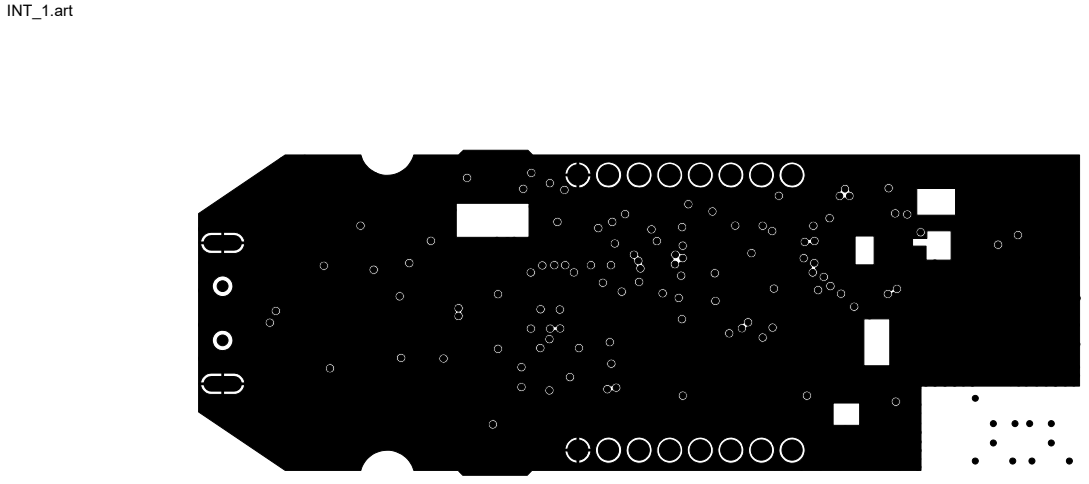
[picture p34: page 6]
INT_1.art

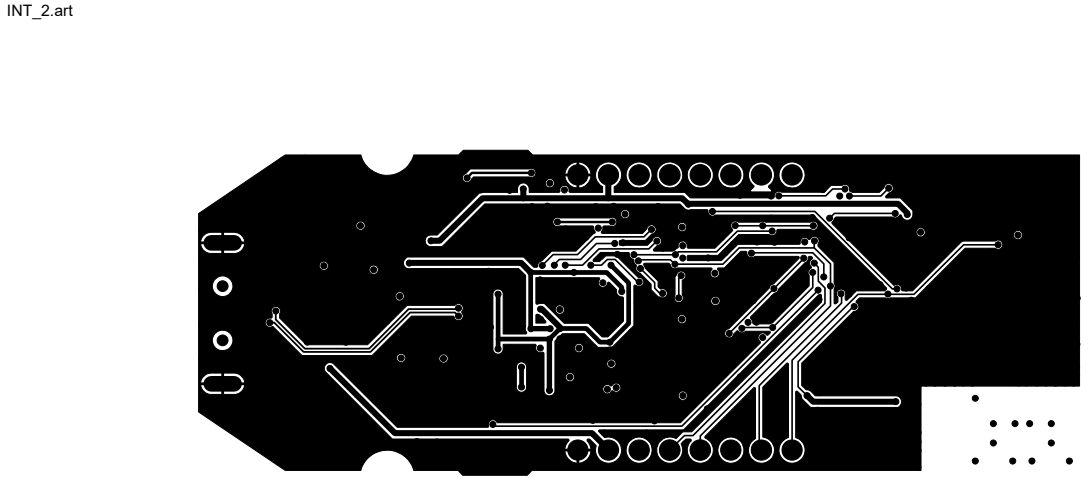
[picture p35: page 7]
INT_2.art

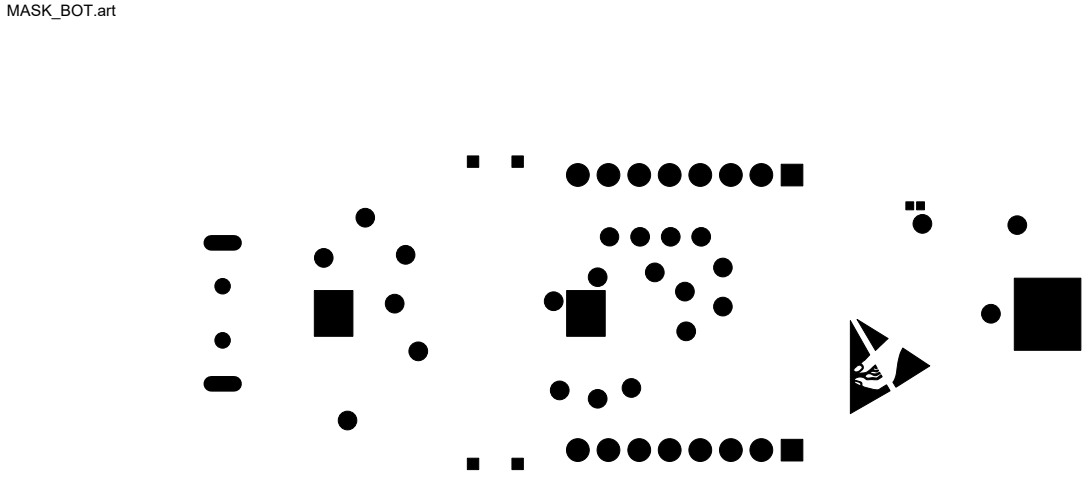
[picture p36: page 8]
MASK_BOT.art

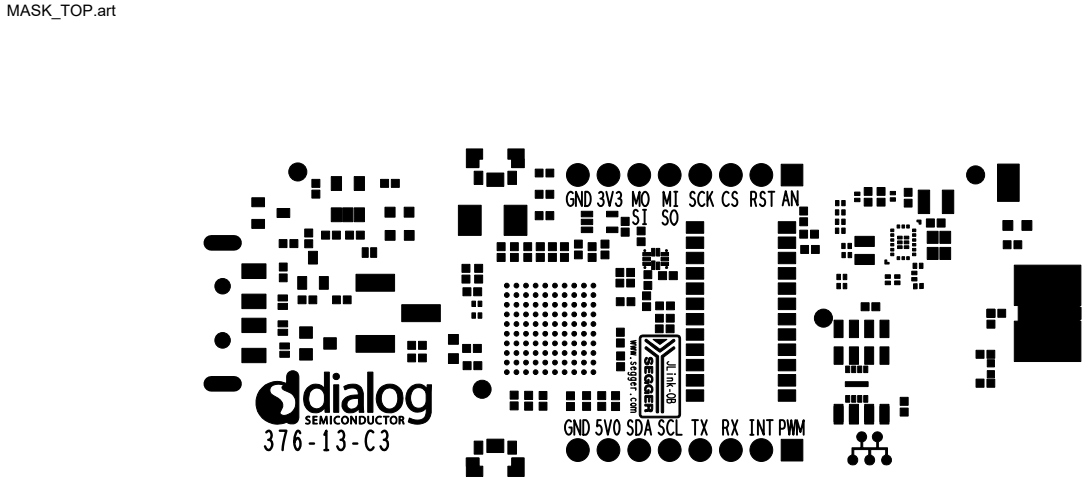
[picture p37: page 9]
MASK_TOP.art

OUTLINE.art

PASTE_BOT.art

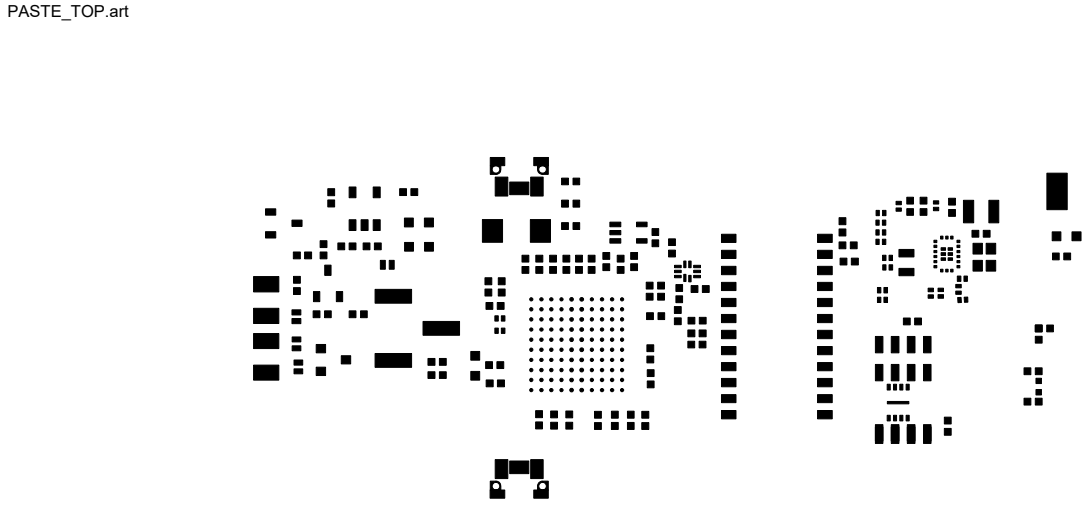
[picture p38: page 12]
PASTE_TOP.art

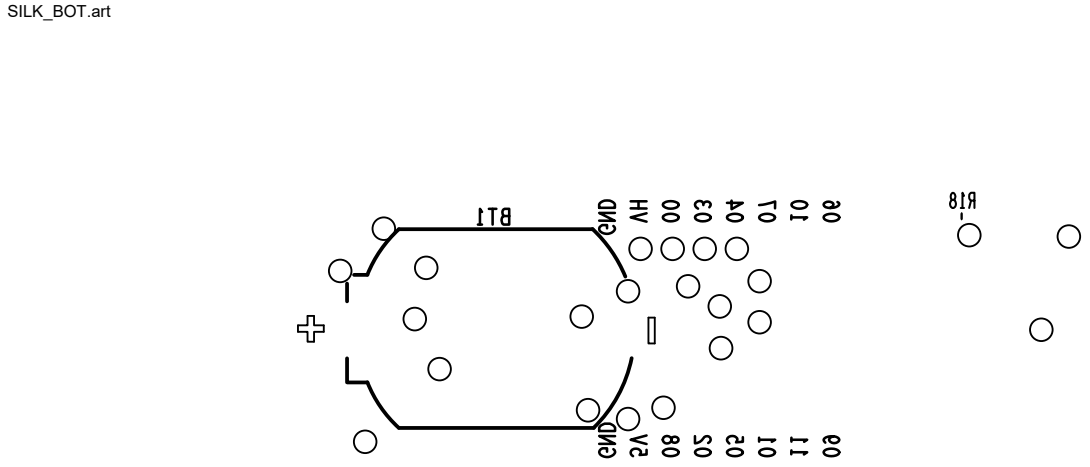
[picture p39: page 13]
SILK_BOT.art

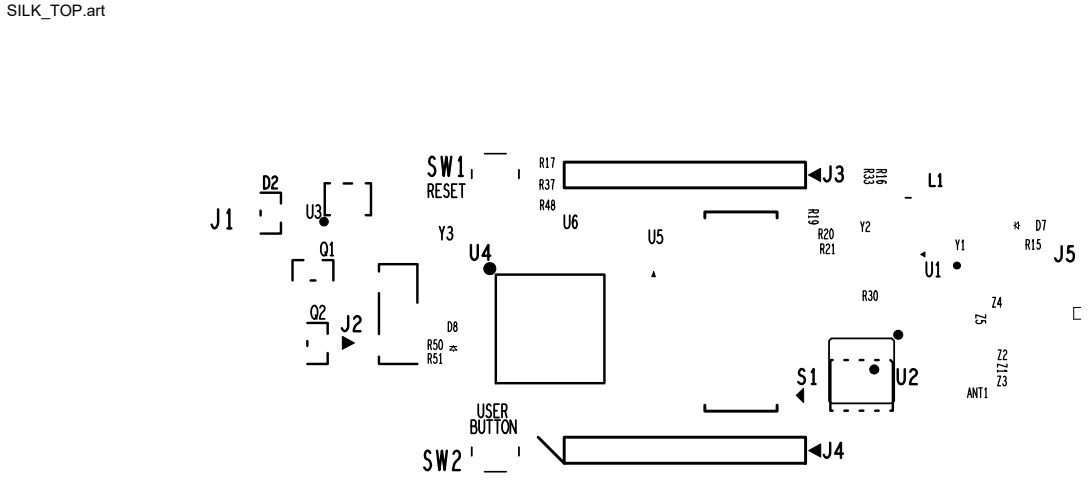
[picture p40: page 14]
SILK_TOP.art

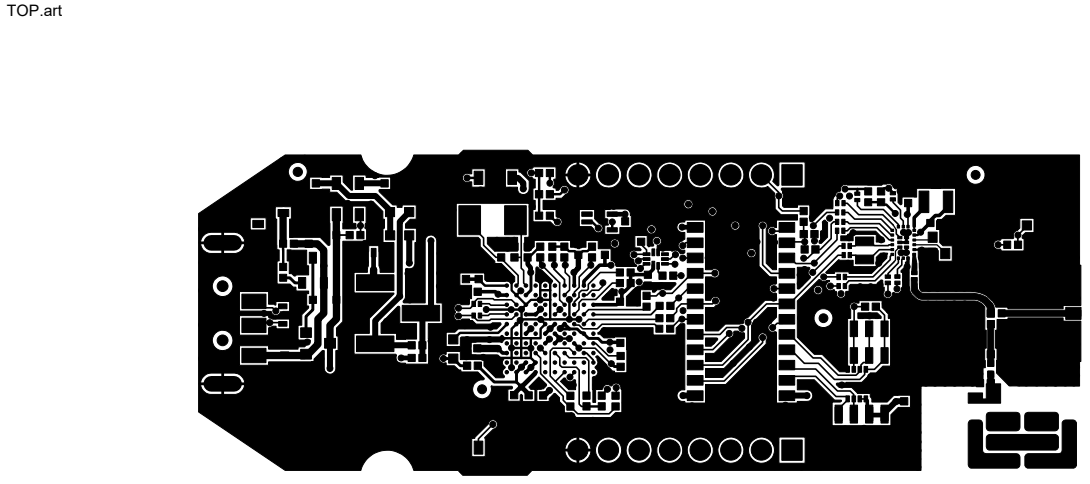
[picture p41: page 15]
TOP.art

d2632-devkt-b-usb_vc3-1-4-np.drl

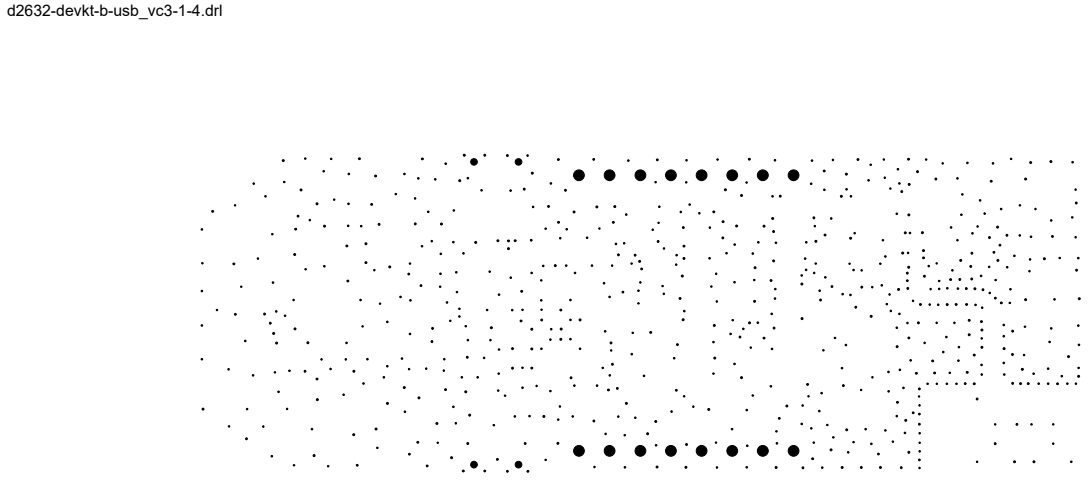
[picture p42: page 17]
d2632-devkt-b-usb_vc3-1-4.drl

d2632-devkt-b-usb_vc3_plated.rou

d2632-devkt-b-usb_vc3.rou
